impatrq/VIA/aplicacion de Gps/codigo final parte 1.jpg

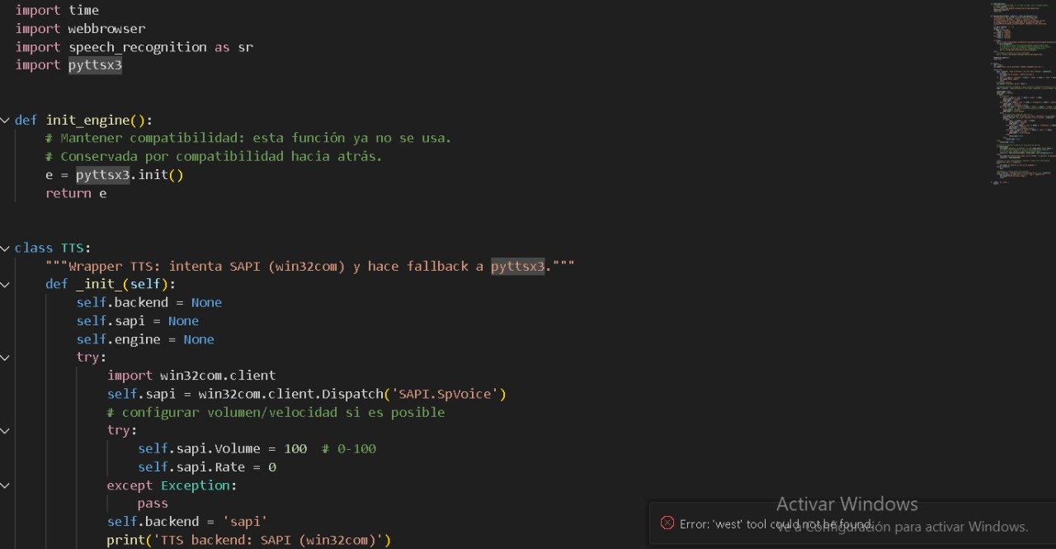
aplicacion de Gps/codigo final parte 1.jpg
