impatrq/VIA/aplicacion de Gps/codigo final parte 2.jpg

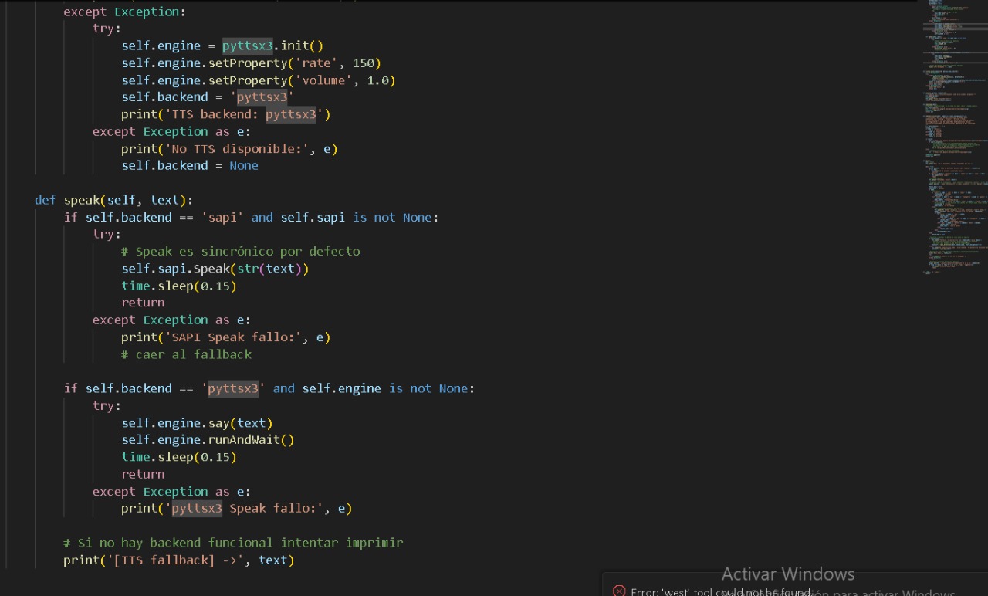
aplicacion de Gps/codigo final parte 2.jpg
