impatrq/VIA/aplicacion de Gps/codigo final parte 3.jpg

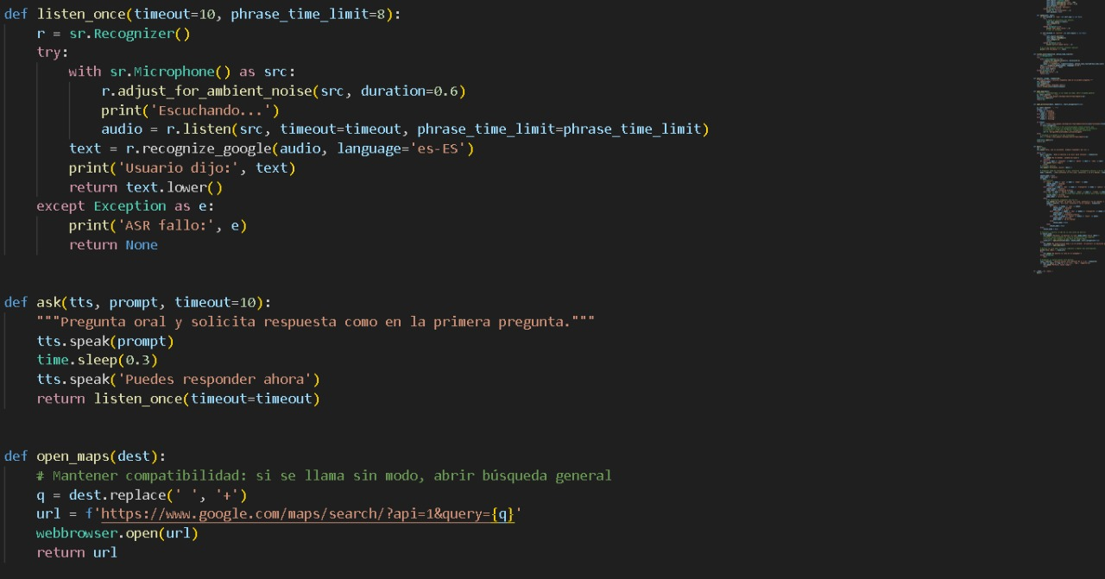
aplicacion de Gps/codigo final parte 3.jpg
