impatrq/VIA/aplicacion de Gps/inicio de codigo principal.jpg

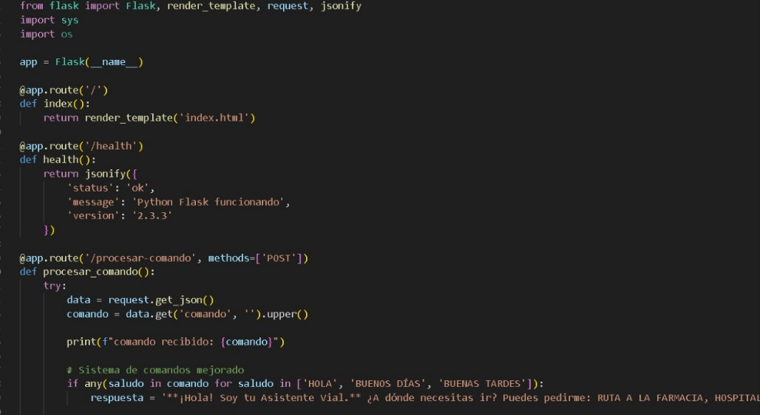
aplicacion de Gps/inicio de codigo principal.jpg
