impatrq/VIA/aplicacion de Gps/segunda parte de codigo principal.jpg

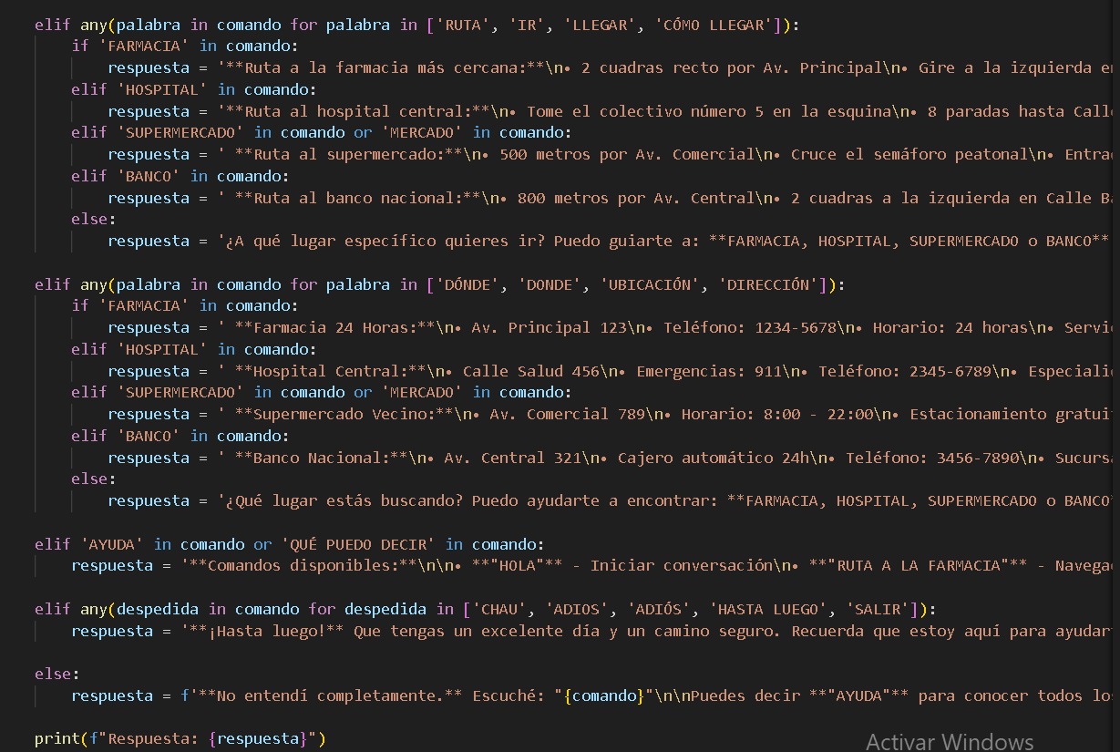
aplicacion de Gps/segunda parte de codigo principal.jpg
