impatrq/VIA/aplicacion de Gps/tercera parte de codigo principal.jpg

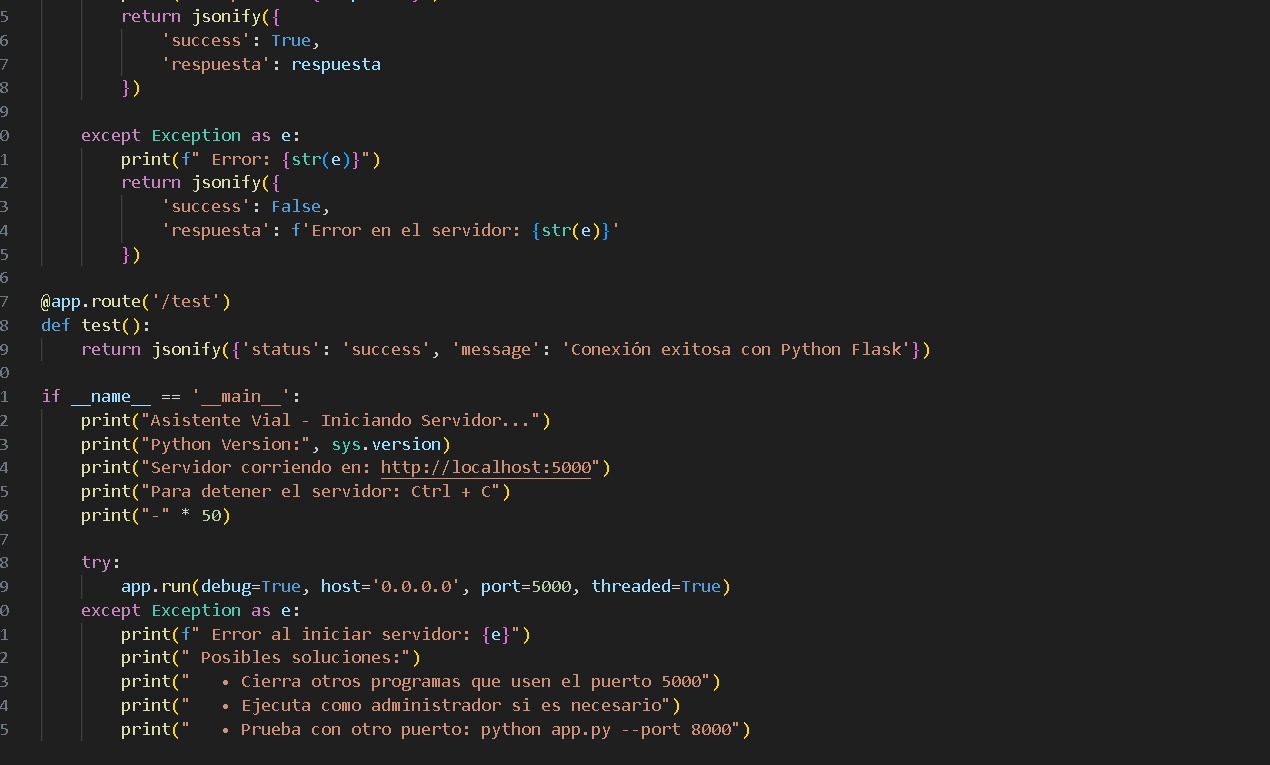
aplicacion de Gps/tercera parte de codigo principal.jpg
