impatrq/VIA/circuito de audio/pongo placa en acido.jpg

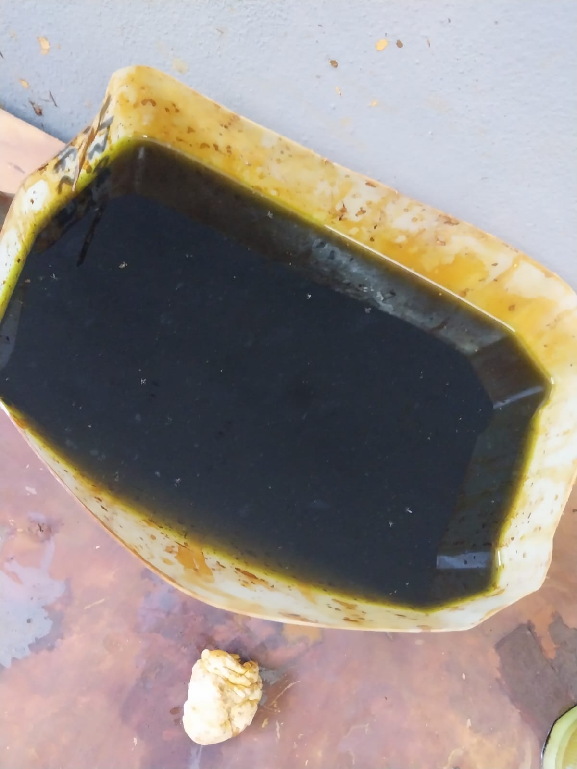
circuito de audio/pongo placa en acido.jpg
