impatrq/VIA/Compras/camara.jpg

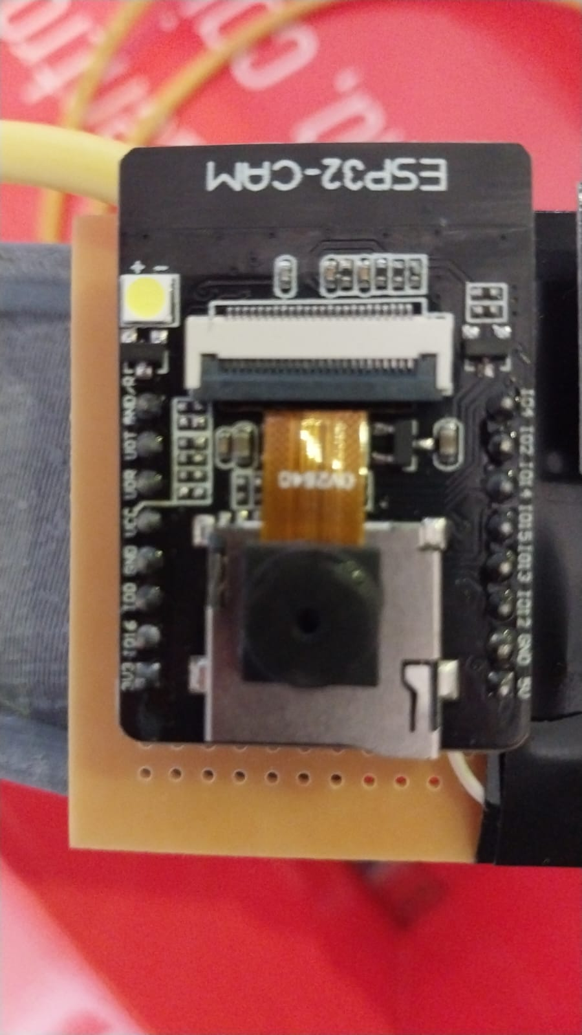
Compras/camara.jpg
