impatrq/VIA/Compras/raspberry.jpg

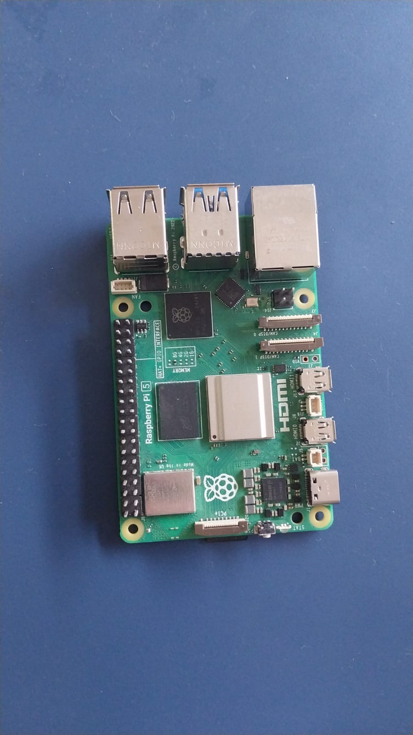
Compras/raspberry.jpg
