impatrq/VIA/Compras/sensor de px.jpg

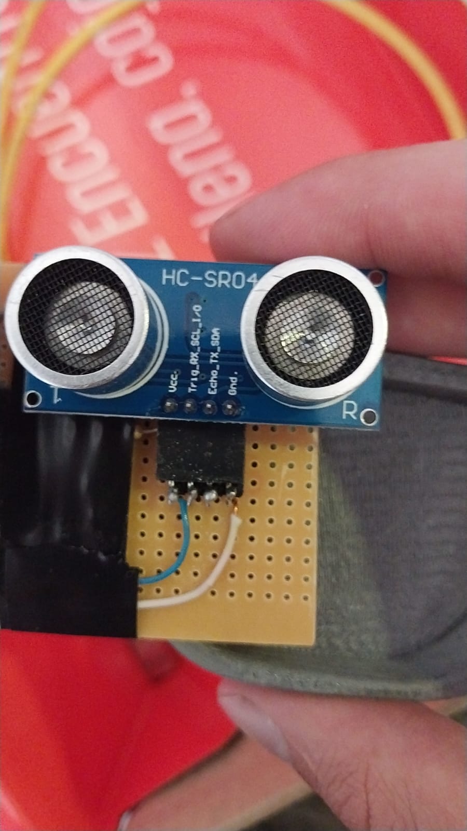
Compras/sensor de px.jpg
