impatrq/VIA/Compras/termocontra.jpg

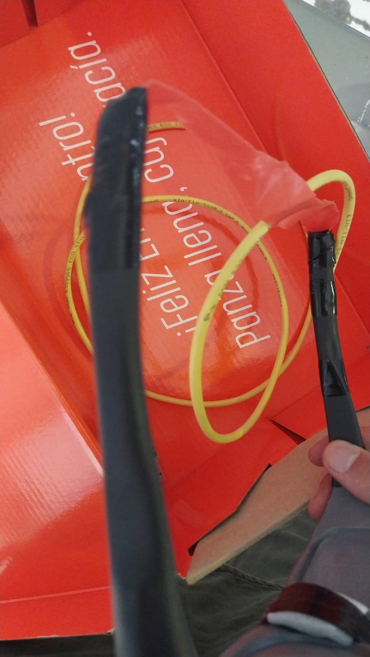
Compras/termocontra.jpg
