impatrq/VIA/Diseño de los lentes/12466696-14f5-42b8-8ee0-9e572aa3d88a.jpeg

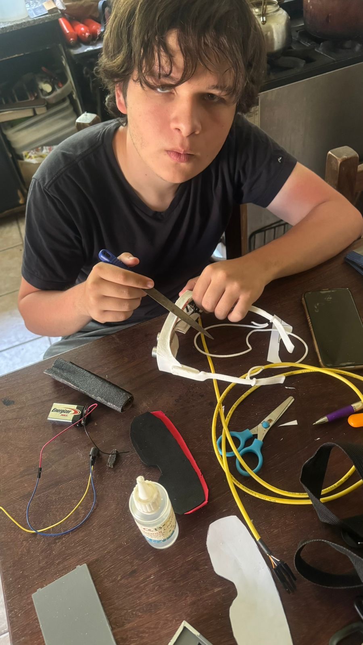
Diseño de los lentes/12466696-14f5-42b8-8ee0-9e572aa3d88a.jpeg
