impatrq/VIA/Diseño de los lentes/b83320ea-6508-4606-a873-f71e1e73f696.jpeg

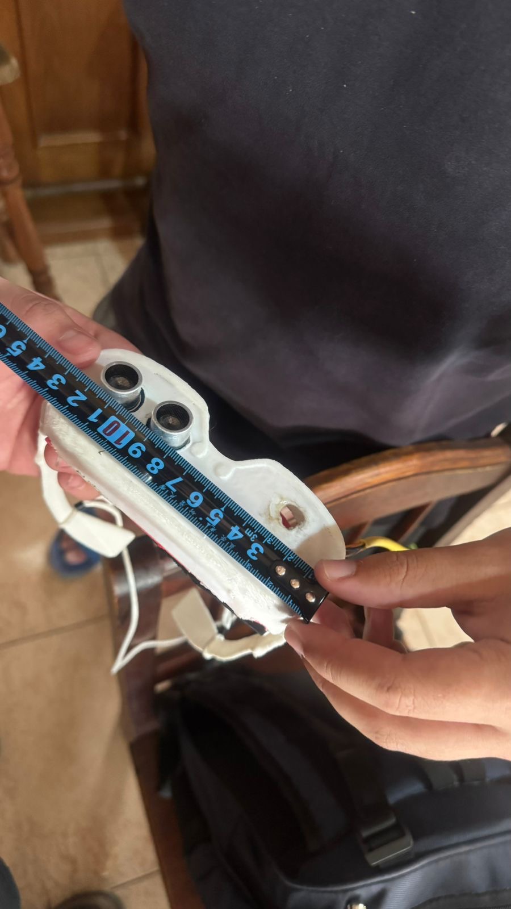
Diseño de los lentes/b83320ea-6508-4606-a873-f71e1e73f696.jpeg
