impatrq/VIA/Diseño de los lentes/primera impresion de lentes.jpg

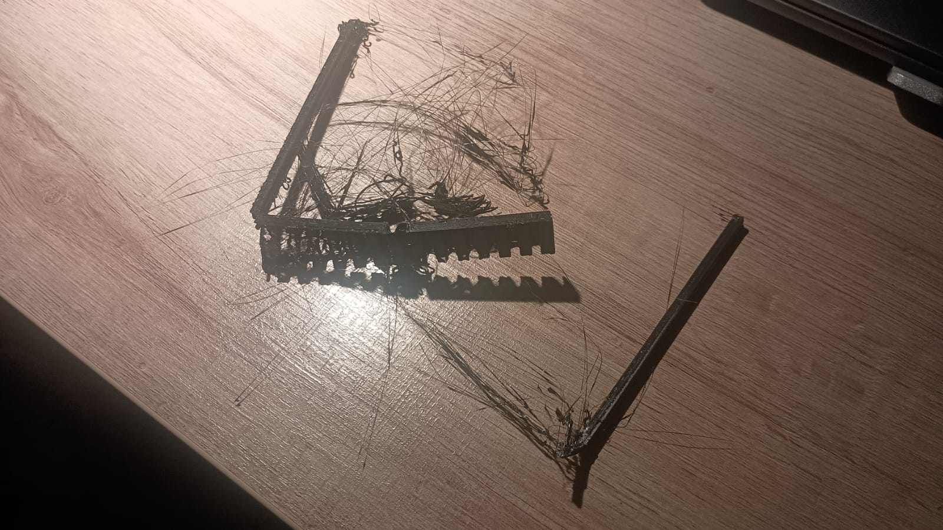
Diseño de los lentes/primera impresion de lentes.jpg
