impatrq/VIA/Diseño de los lentes/quinto diseño de lentes.jpg

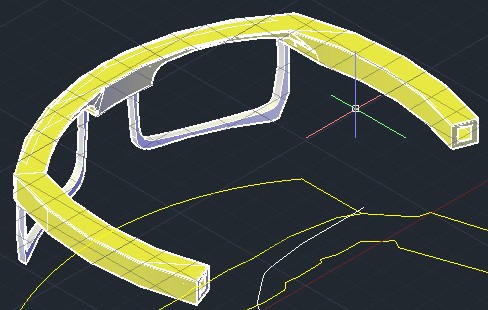
Diseño de los lentes/quinto diseño de lentes.jpg
