impatrq/VIA/Diseño de los lentes/sexto diseño de lentes.jpg

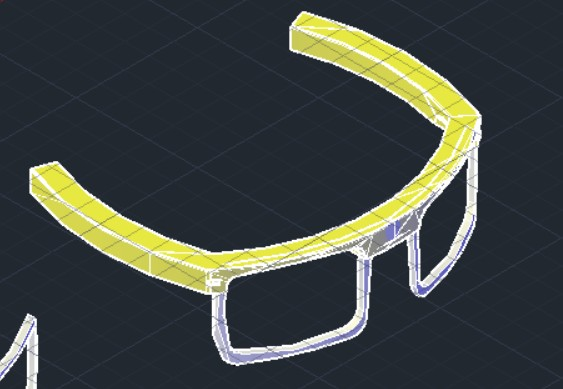
Diseño de los lentes/sexto diseño de lentes.jpg
