impatrq/VIA/Diseño de los lentes/visagras de lentes.jpg

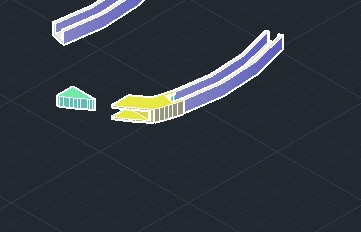
Diseño de los lentes/visagras de lentes.jpg
