impatrq/VIA/Imagenes/Auriculares/90 sin título_20251203141430.jpeg

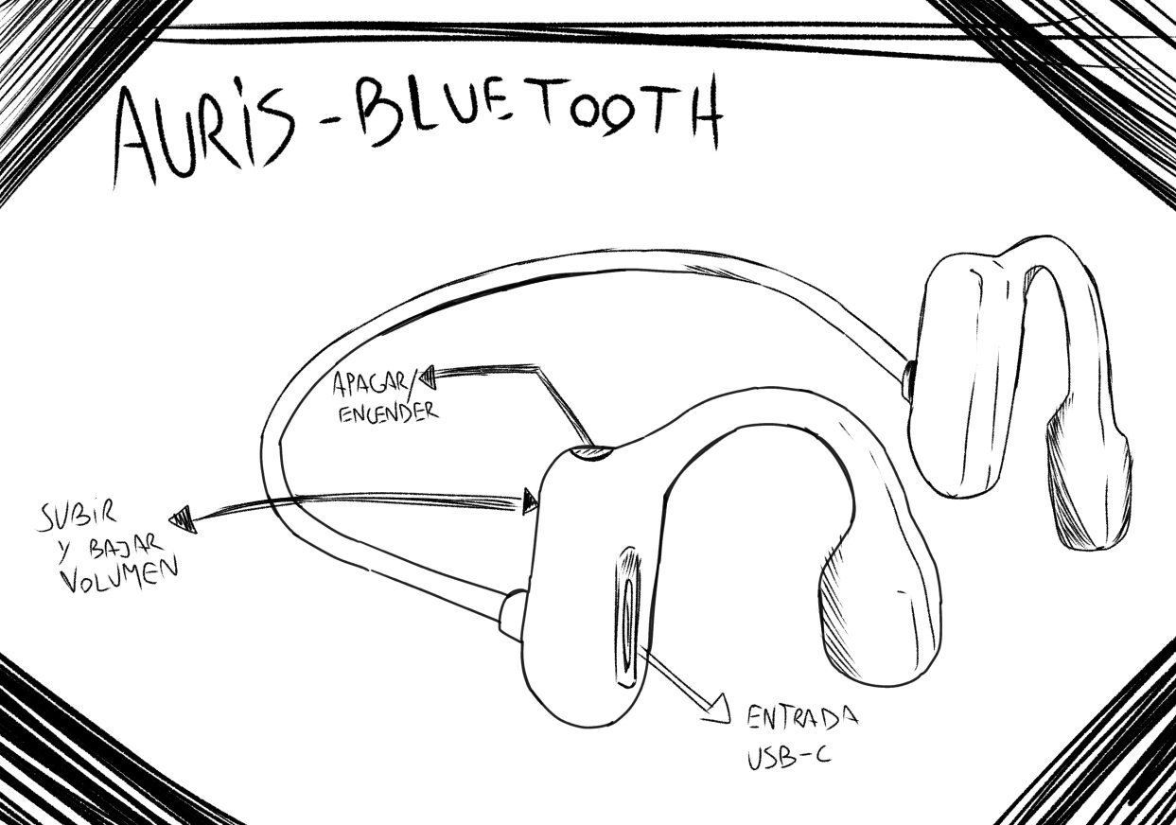
Imagenes/Auriculares/90 sin título_20251203141430.jpeg
