impatrq/VIA/Imagenes/Auriculares/WhatsApp Image 2025-12-07 at 10.33.51 PM.jpeg

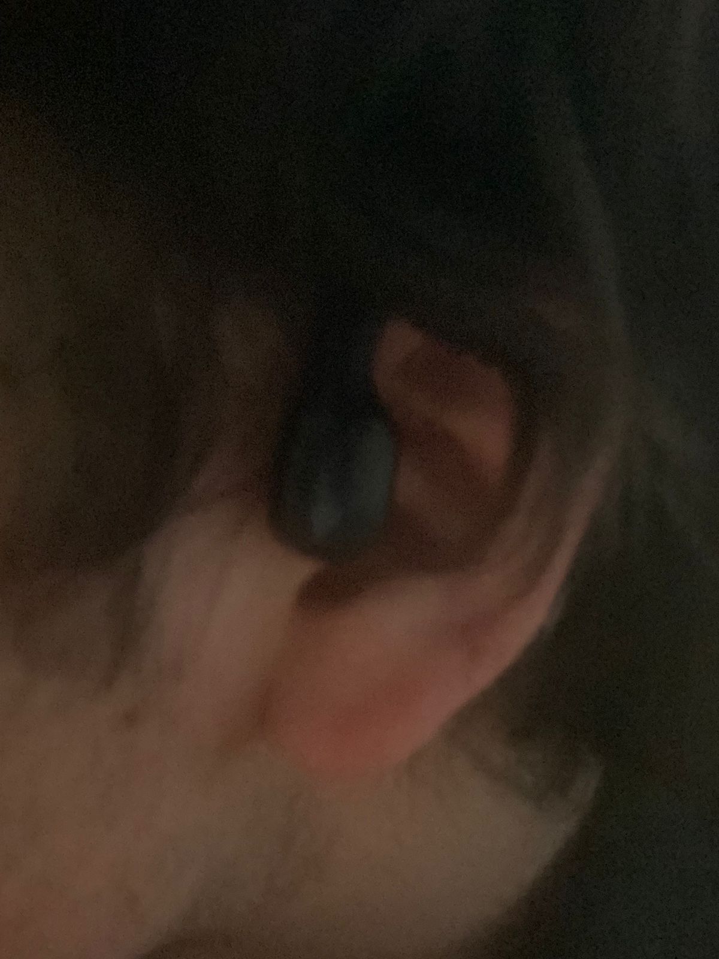
Imagenes/Auriculares/WhatsApp Image 2025-12-07 at 10.33.51 PM.jpeg
