impatrq/VIA/Imagenes/Camara/Camara.jpg

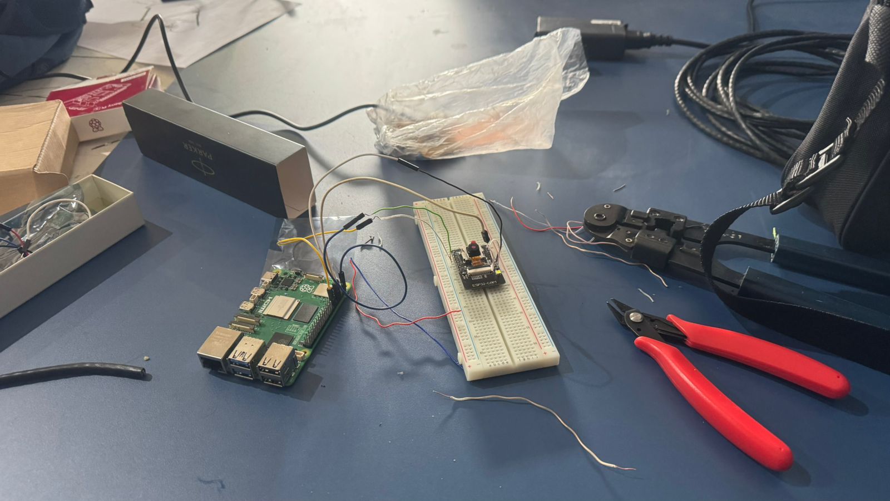
Imagenes/Camara/Camara.jpg
