impatrq/VIA/Imagenes/Foto del grupo/Bautista Paz.png

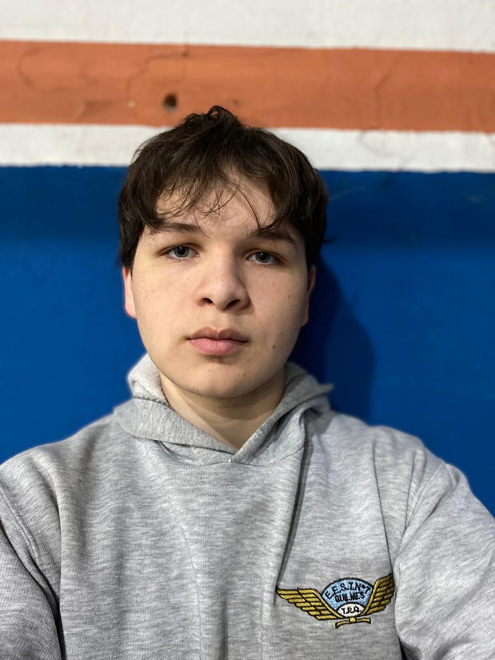
Imagenes/Foto del grupo/Bautista Paz.png
