impatrq/VIA/Imagenes/Foto del grupo/Caram Matias.png

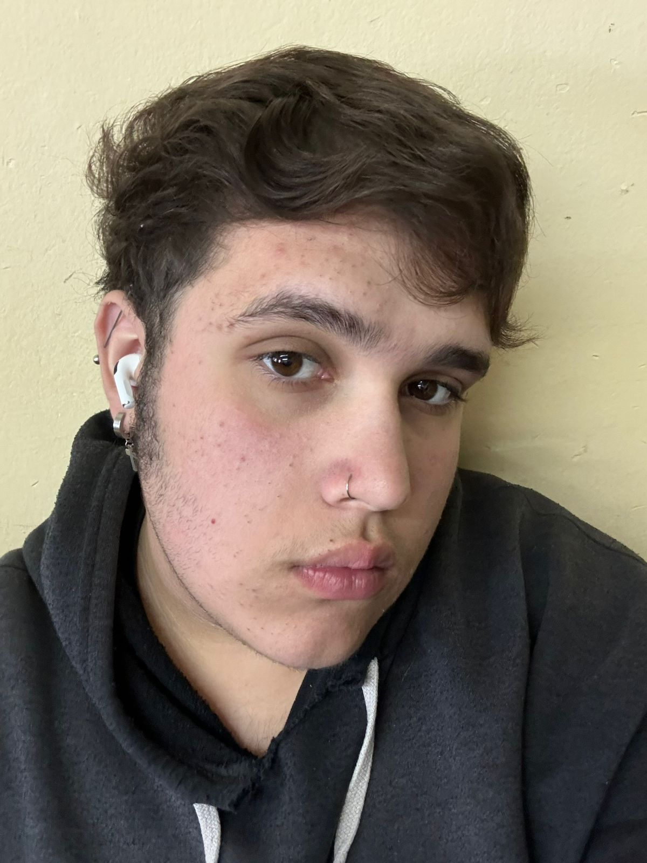
Imagenes/Foto del grupo/Caram Matias.png
