impatrq/VIA/Imagenes/Foto del grupo/Foto grupal del dia de la expo .jpg

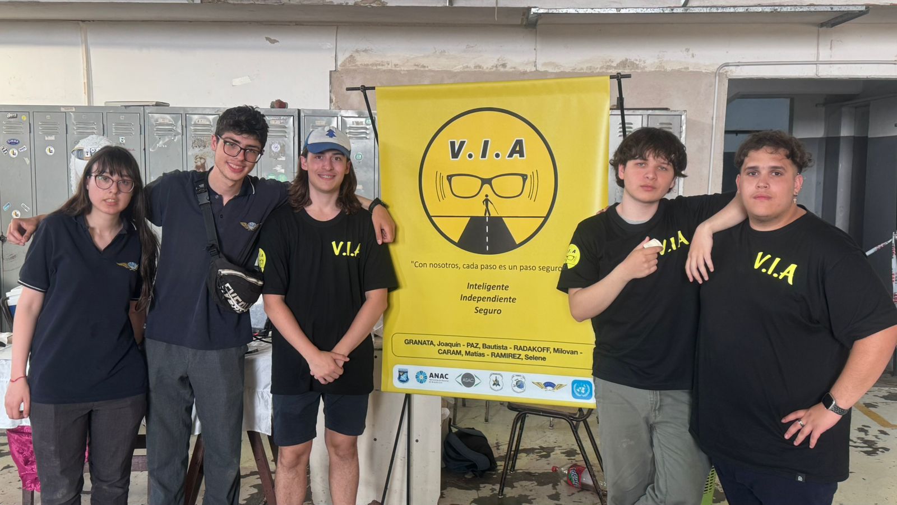
Imagenes/Foto del grupo/Foto grupal del dia de la expo .jpg
