impatrq/VIA/Imagenes/Foto del grupo/Granata Joaquin.png

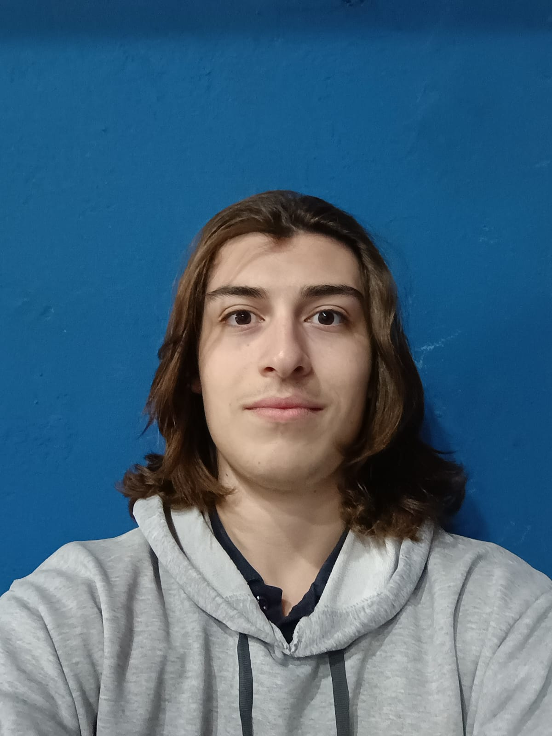
Imagenes/Foto del grupo/Granata Joaquin.png
