impatrq/VIA/Imagenes/Foto del grupo/Radakoff Milovan.png

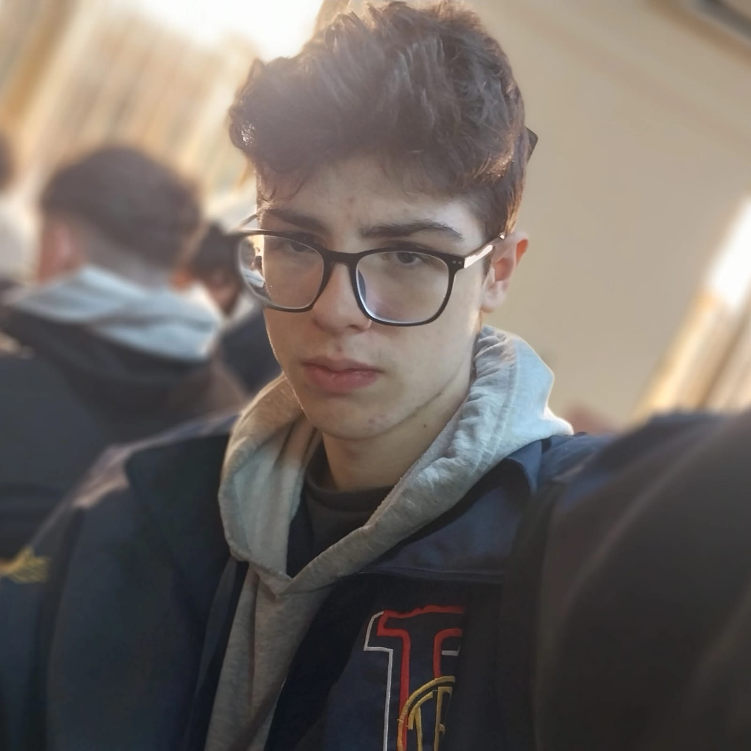
Imagenes/Foto del grupo/Radakoff Milovan.png
