impatrq/VIA/Imagenes/Lentes/Corte de filamento en la reimpresion 2.3.jpg

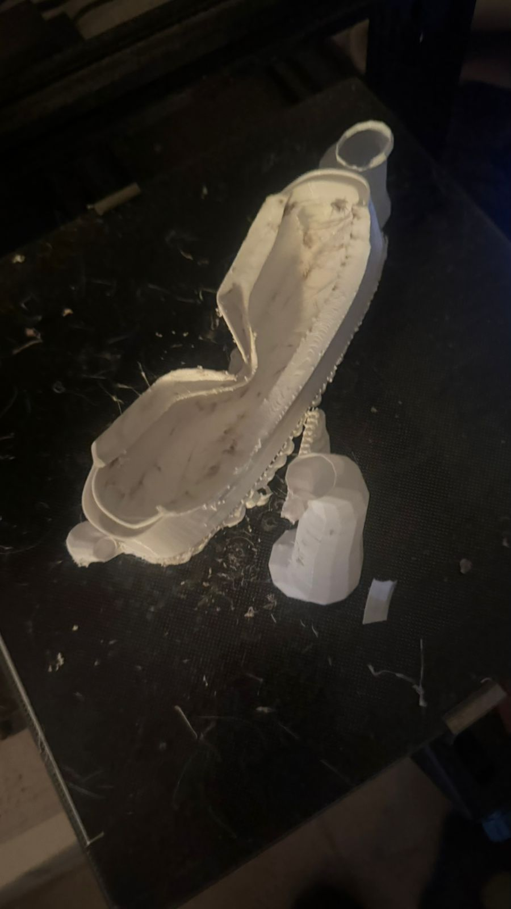
Imagenes/Lentes/Corte de filamento en la reimpresion 2.3.jpg
