impatrq/VIA/Imagenes/Lentes/Fallo de la 1ra impresion.jpg

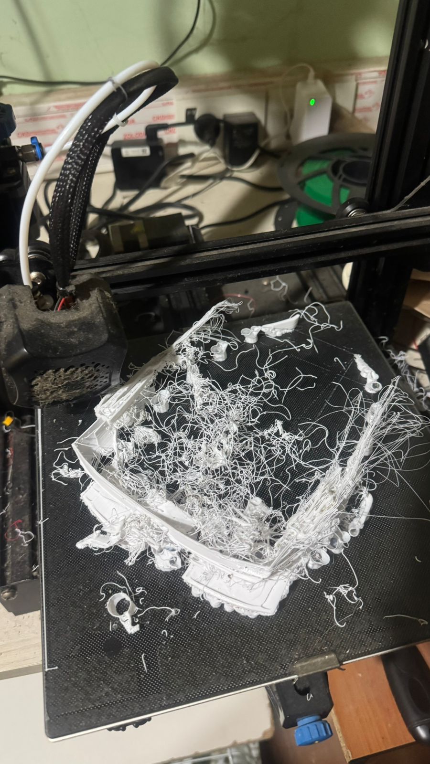
Imagenes/Lentes/Fallo de la 1ra impresion.jpg
