impatrq/VIA/Imagenes/Lentes/Fallo impresion 3.0.jpg

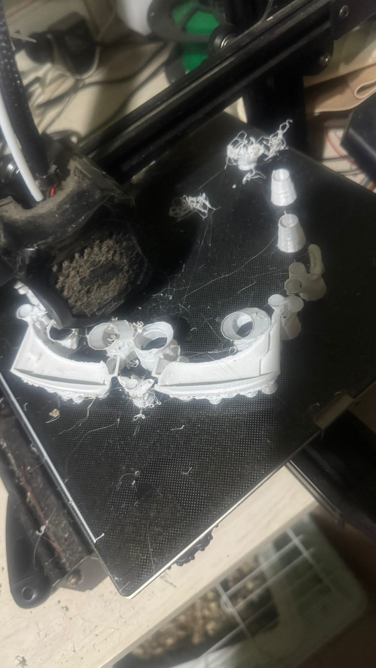
Imagenes/Lentes/Fallo impresion 3.0.jpg
