impatrq/VIA/Imagenes/Lentes/image.png

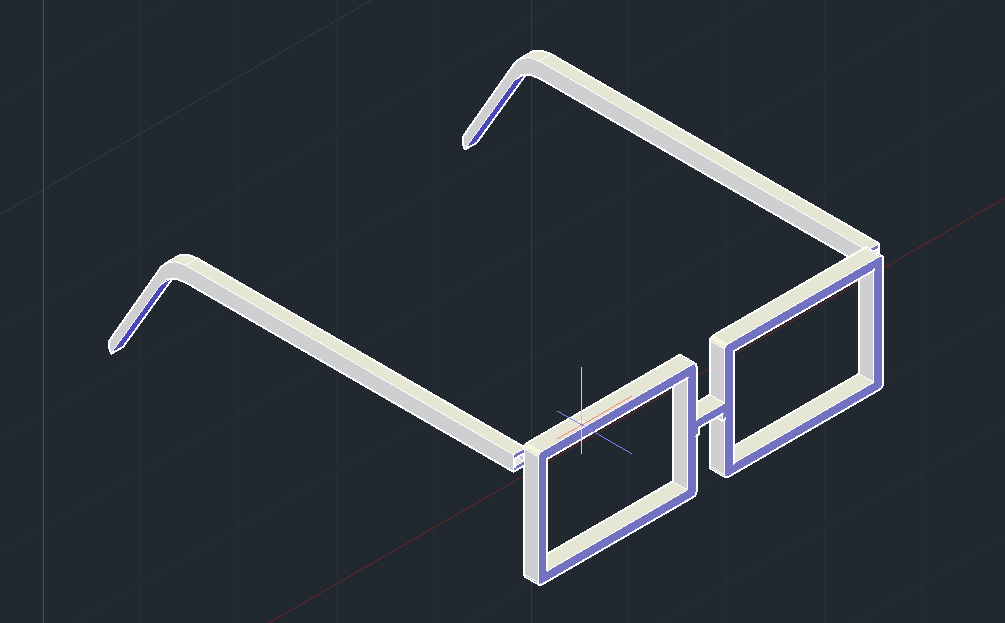
Imagenes/Lentes/image.png
