impatrq/VIA/Imagenes/Lentes/Impresion modelo 2.3.jpg

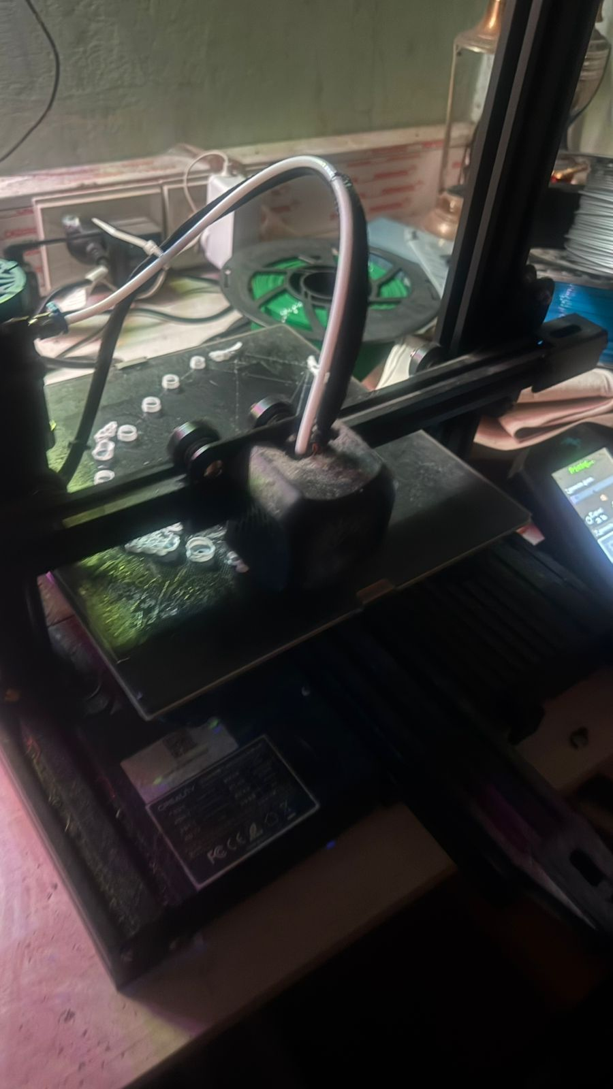
Imagenes/Lentes/Impresion modelo 2.3.jpg
