impatrq/VIA/Imagenes/Lentes/Lentes V2.1 - Puestos.png

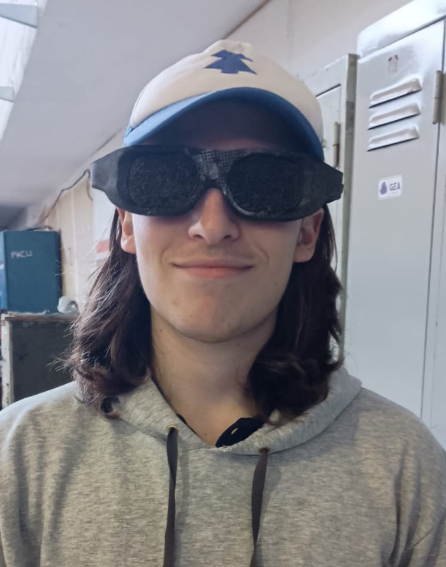
Imagenes/Lentes/Lentes V2.1 - Puestos.png
