impatrq/VIA/Imagenes/Lentes/Lentes V2.1.png

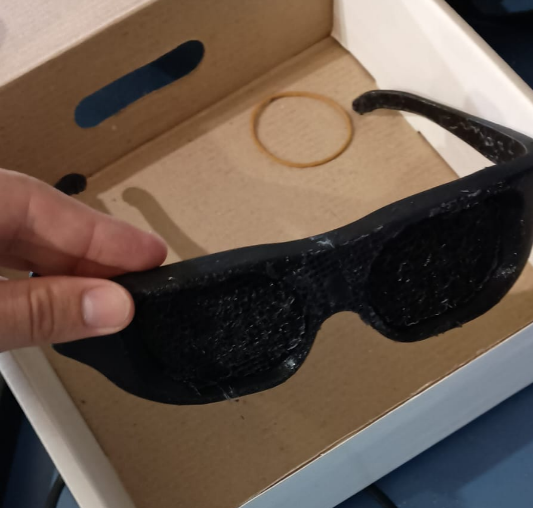
Imagenes/Lentes/Lentes V2.1.png
