impatrq/VIA/Imagenes/Lentes/Lentes V2.2.jpg

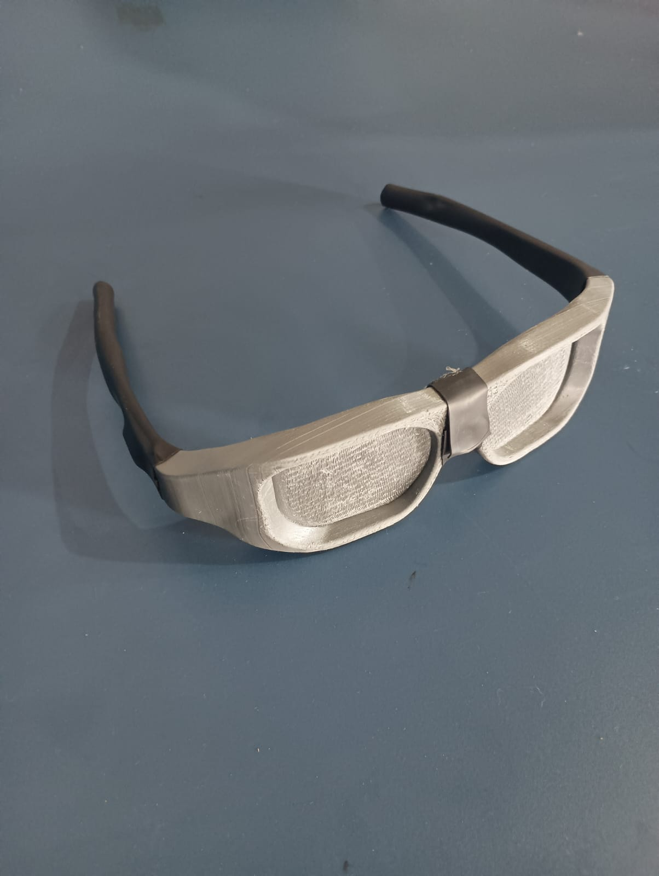
Imagenes/Lentes/Lentes V2.2.jpg
