impatrq/VIA/Imagenes/Lentes/Lentes v2.3 terminados.jpg

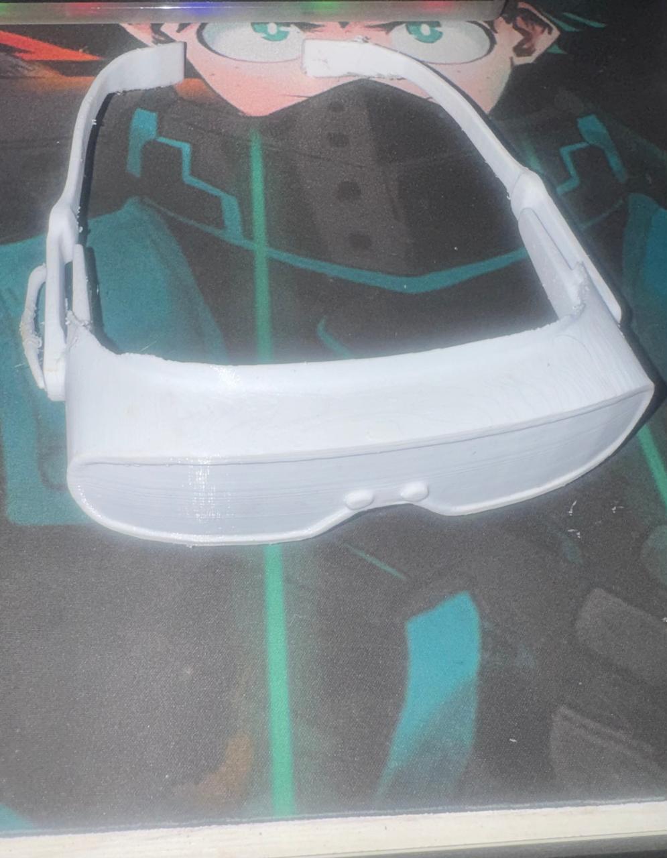
Imagenes/Lentes/Lentes v2.3 terminados.jpg
