impatrq/VIA/Imagenes/Lentes/Modelado de la caja.png

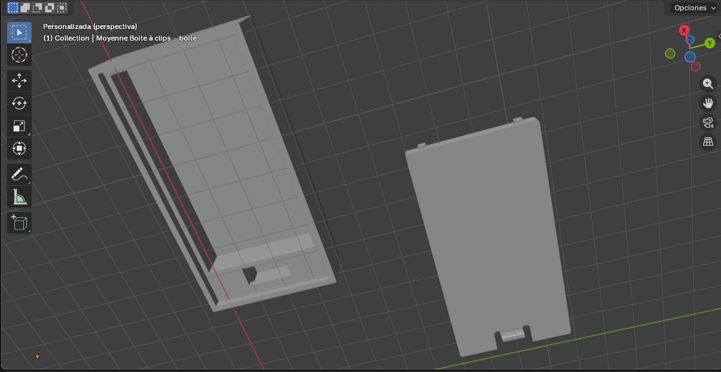
Imagenes/Lentes/Modelado de la caja.png
