impatrq/VIA/Imagenes/Lentes/Modelado de los lentes.png

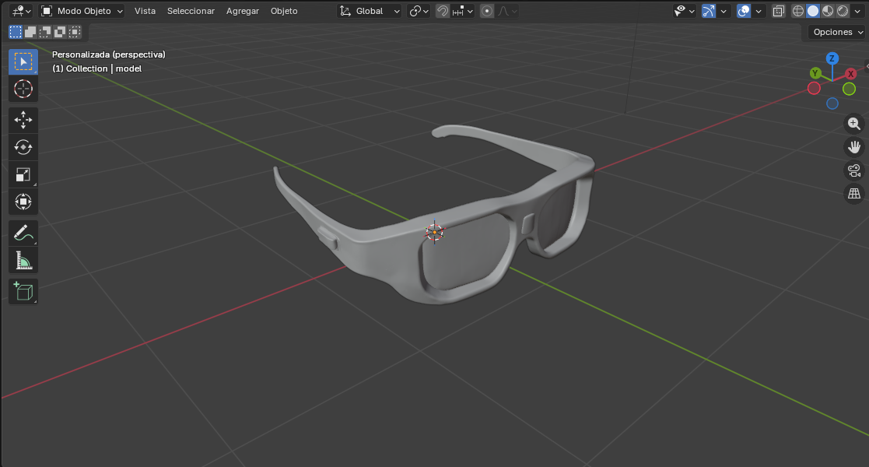
Imagenes/Lentes/Modelado de los lentes.png
