impatrq/VIA/Imagenes/Lentes/Modelo 2.3 reimprecion.png

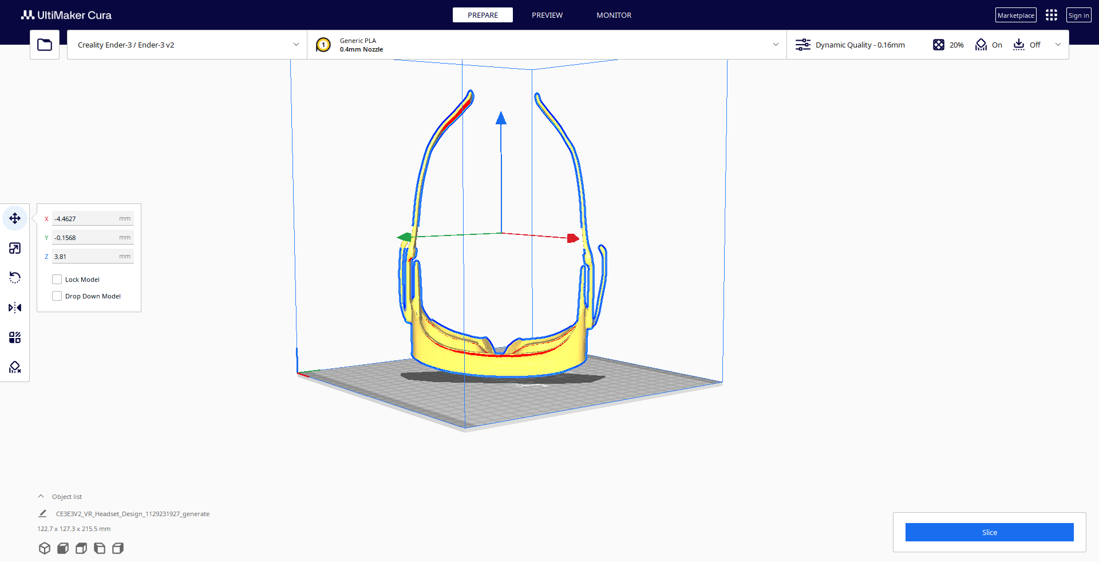
Imagenes/Lentes/Modelo 2.3 reimprecion.png
