impatrq/VIA/Imagenes/Lentes/Modelo 2.3.png

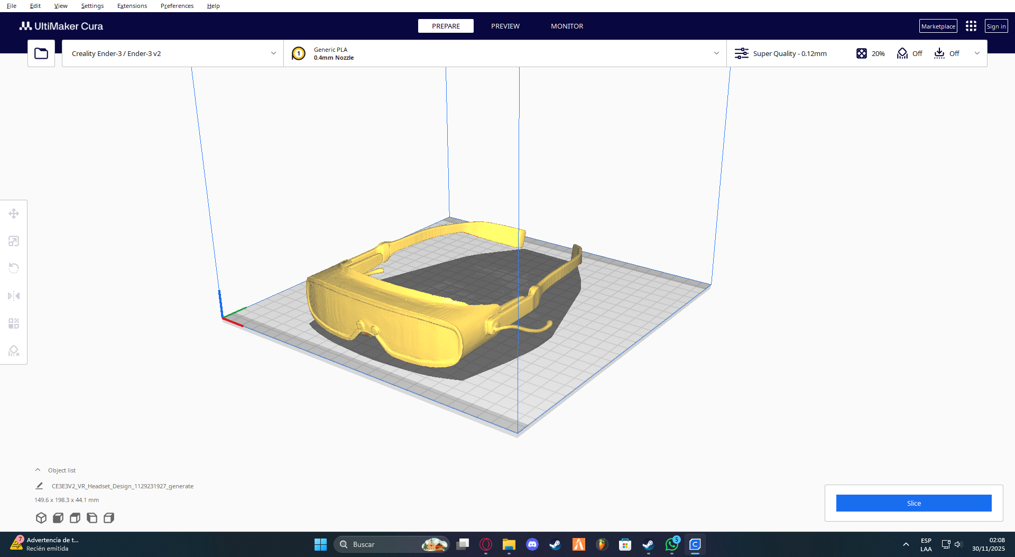
Imagenes/Lentes/Modelo 2.3.png
