impatrq/VIA/Imagenes/Lentes/Modelo 3.0.png

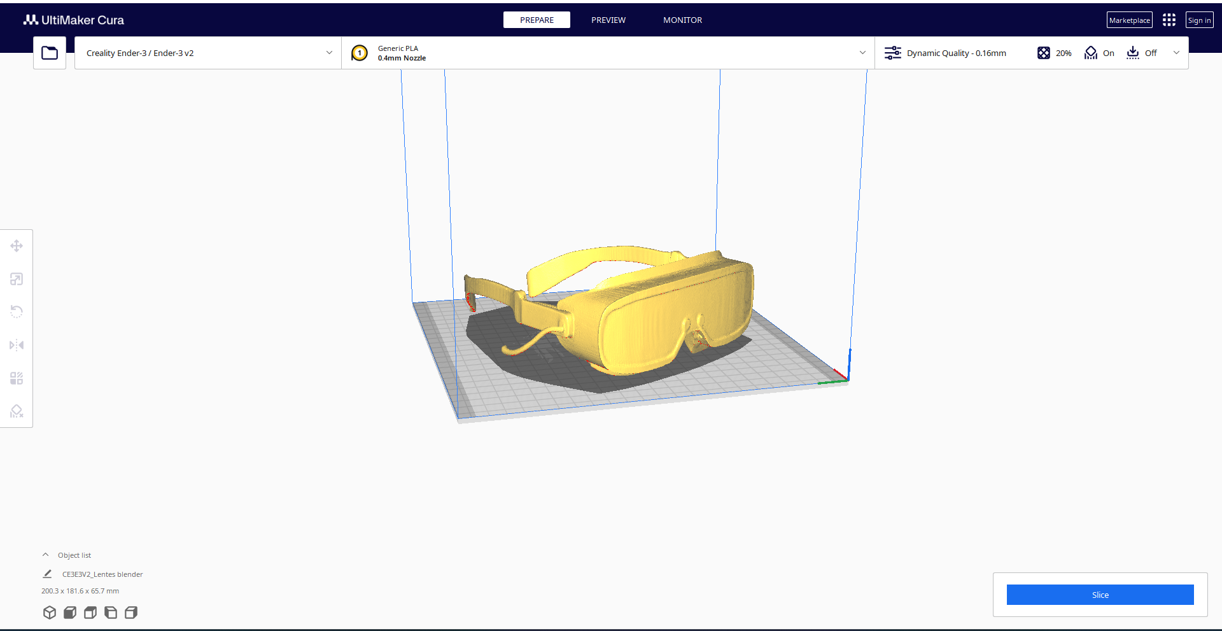
Imagenes/Lentes/Modelo 3.0.png
