impatrq/VIA/Imagenes/Lentes/Modelo terminado v2.3.png

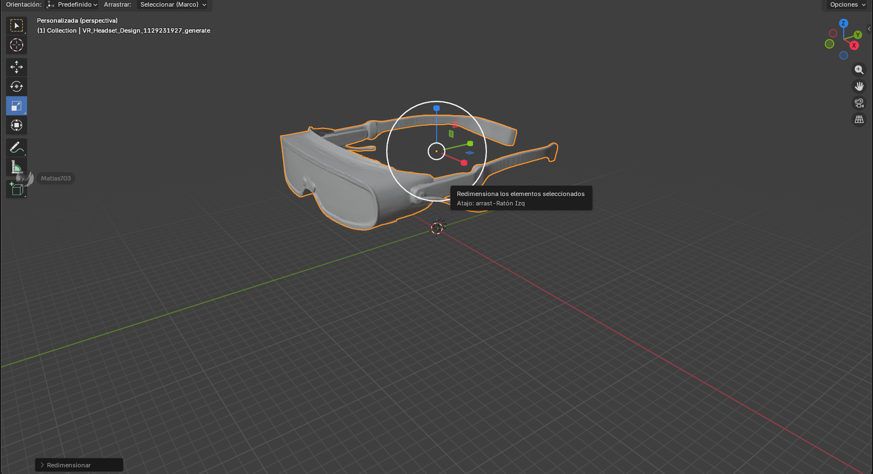
Imagenes/Lentes/Modelo terminado v2.3.png
