impatrq/VIA/Imagenes/Lentes/Modelo terminado v3.0.png

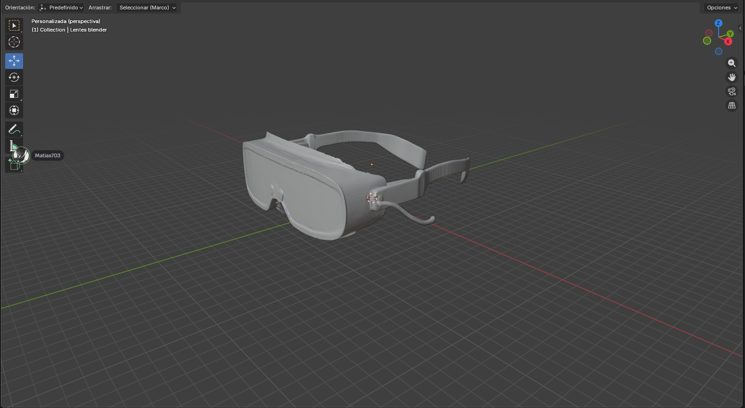
Imagenes/Lentes/Modelo terminado v3.0.png
