impatrq/VIA/Imagenes/Lentes/Nuevo inicio 3.0.jpg

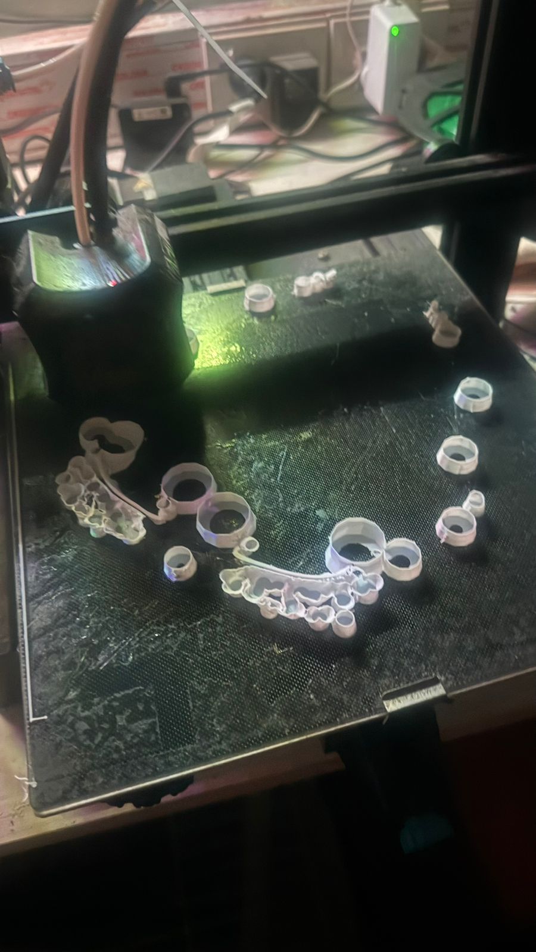
Imagenes/Lentes/Nuevo inicio 3.0.jpg
