impatrq/VIA/Imagenes/Lentes/Reimpresion modelo 2.3.jpg

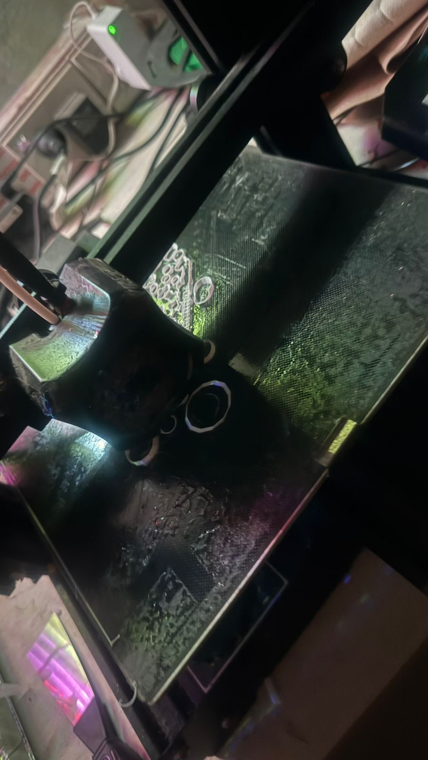
Imagenes/Lentes/Reimpresion modelo 2.3.jpg
