impatrq/VIA/Imagenes/Lentes/WhatsApp Image 2025-11-18 at 2.41.04 PM.jpeg

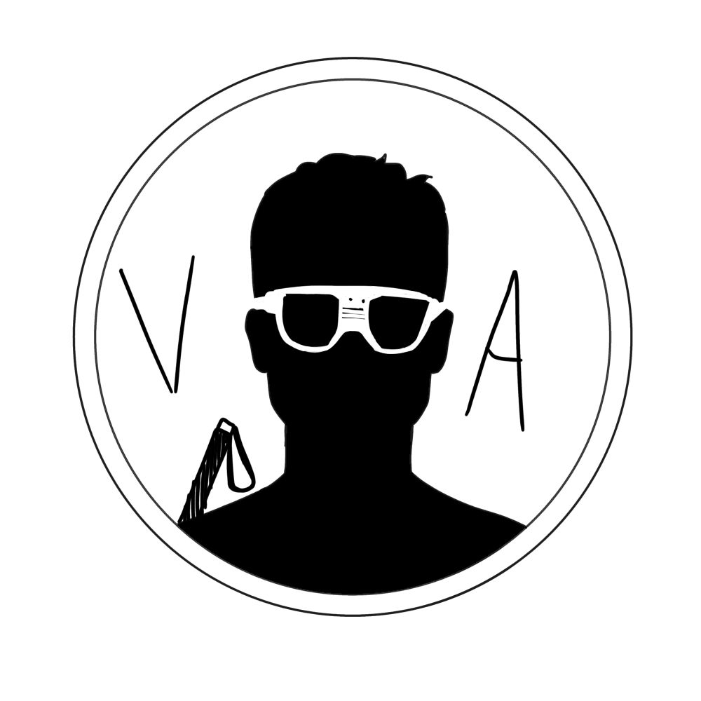
Imagenes/Lentes/WhatsApp Image 2025-11-18 at 2.41.04 PM.jpeg
