impatrq/VIA/Imagenes/Lentes/WhatsApp Image 2025-11-18 at 4.18.59 PM.jpeg

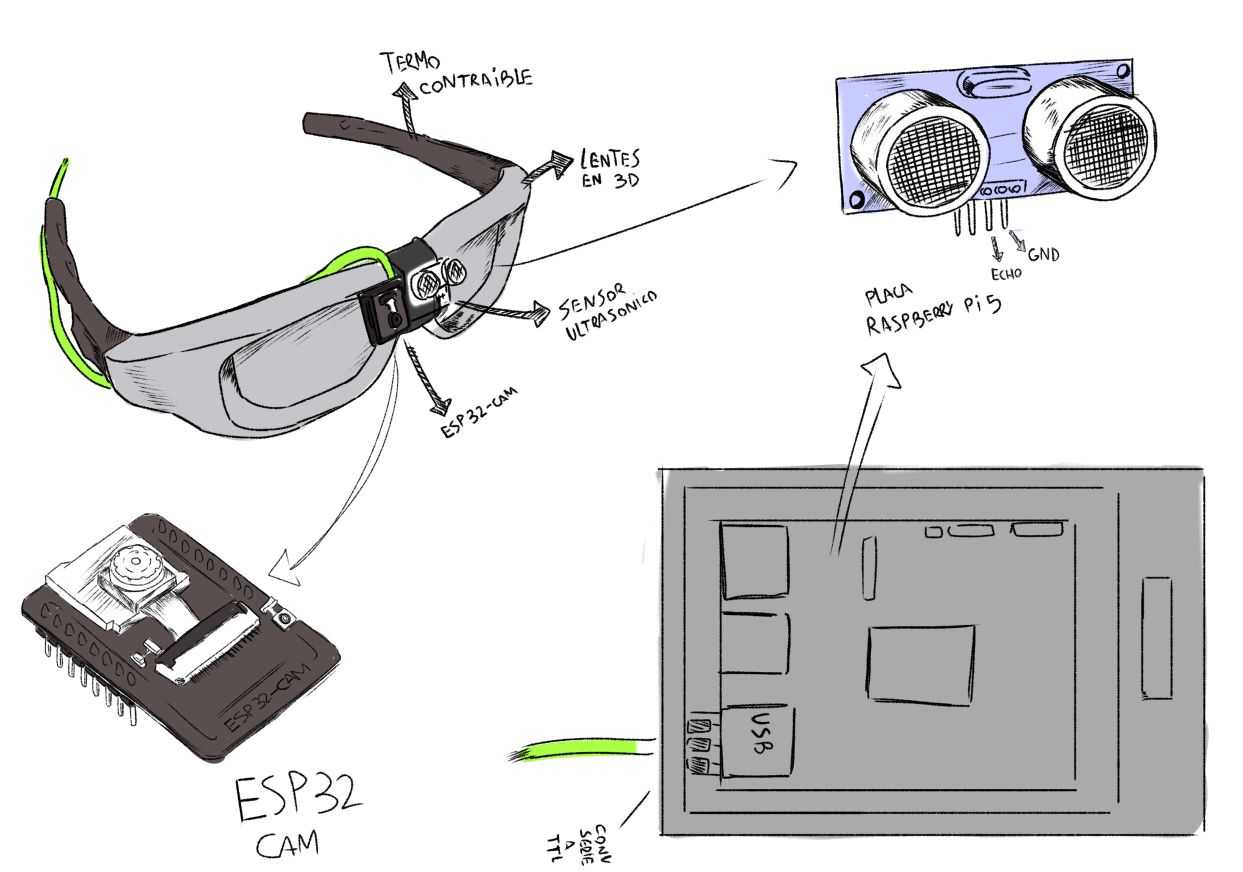
Imagenes/Lentes/WhatsApp Image 2025-11-18 at 4.18.59 PM.jpeg
