impatrq/VIA/Imagenes/Pagina web y de asistencia/Asistencia (A futuro)/BE MY EYES.jpg

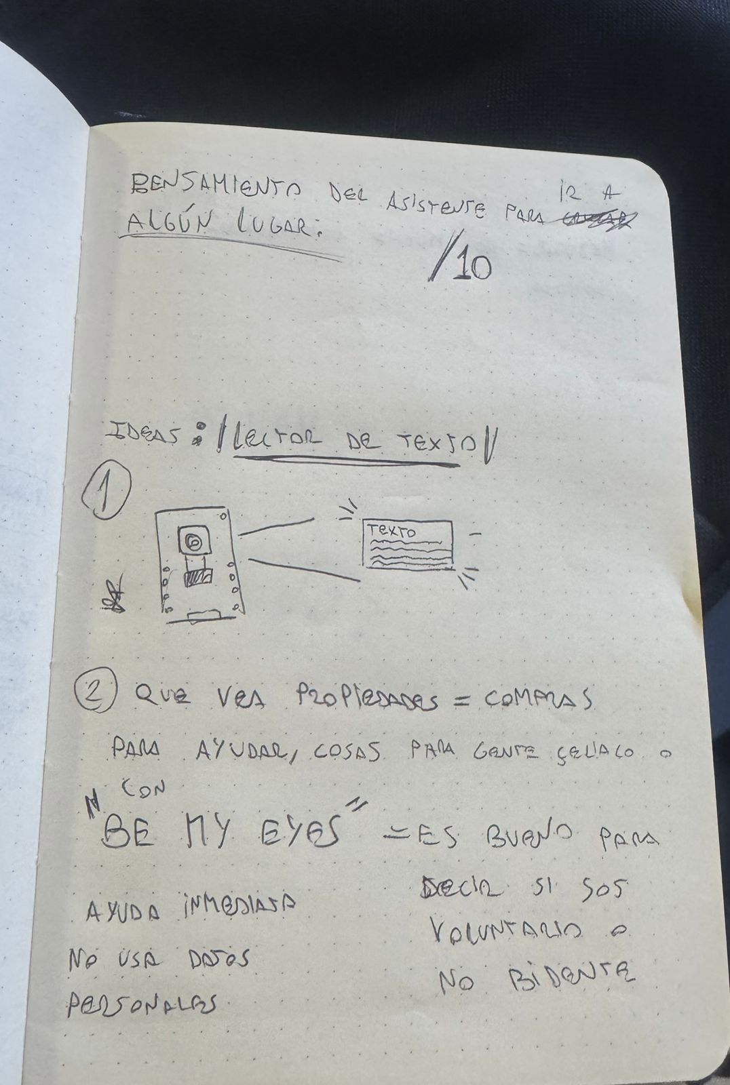
Imagenes/Pagina web y de asistencia/Asistencia (A futuro)/BE MY EYES.jpg
