impatrq/VIA/Imagenes/Pagina web y de asistencia/Pagian de asistencia/Interfaz Area de acción.png

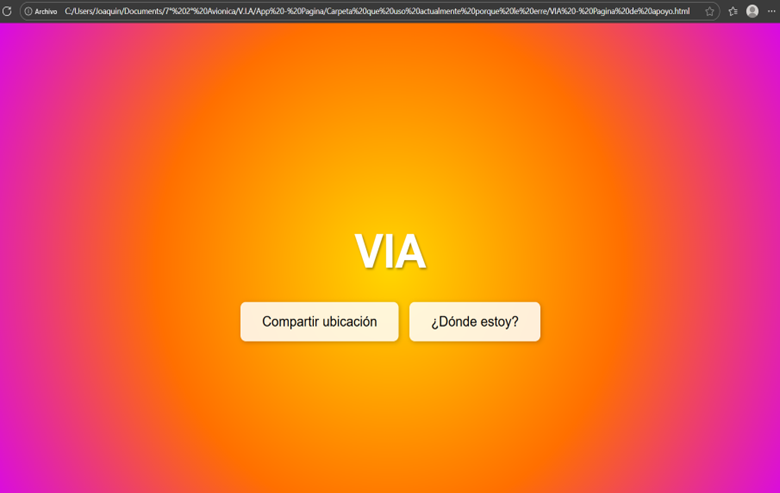
Imagenes/Pagina web y de asistencia/Pagian de asistencia/Interfaz Area de acción.png
