impatrq/VIA/Imagenes/Pagina web y de asistencia/Pagian Web/Apartado de agradecimiento.png

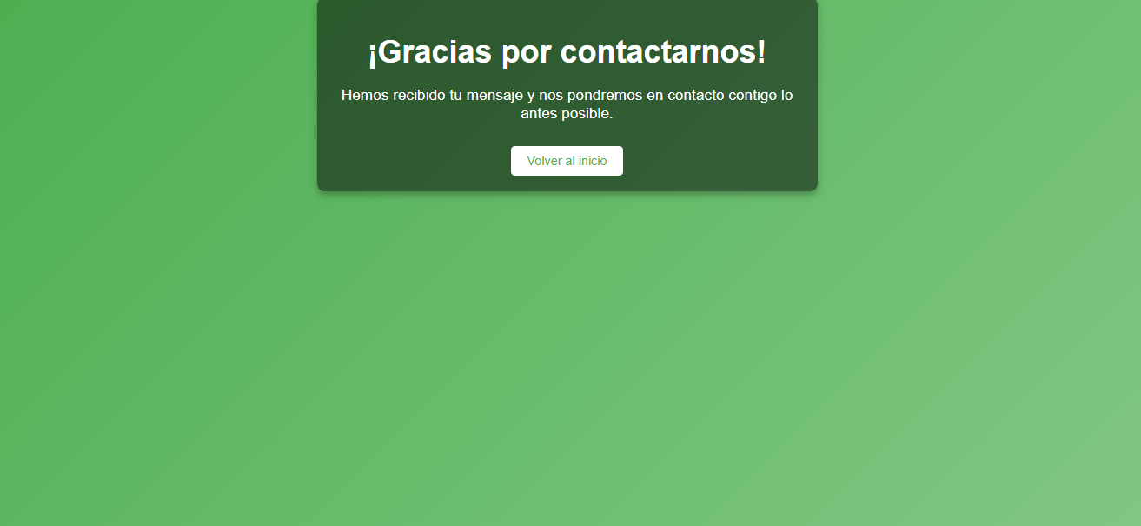
Imagenes/Pagina web y de asistencia/Pagian Web/Apartado de agradecimiento.png
