impatrq/VIA/Imagenes/Pagina web y de asistencia/Pagian Web/Apartado de contacto.png

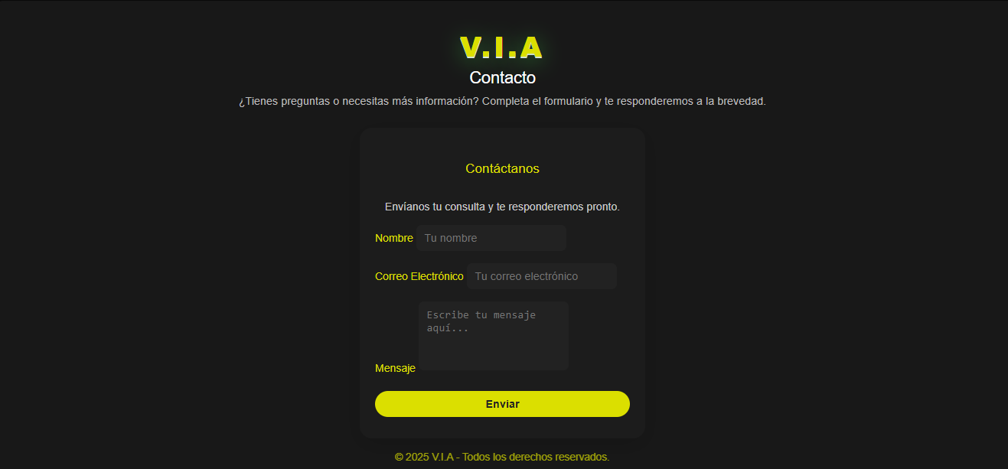
Imagenes/Pagina web y de asistencia/Pagian Web/Apartado de contacto.png
