impatrq/VIA/Imagenes/Pagina web y de asistencia/Pagian Web/Apartado de producto.png

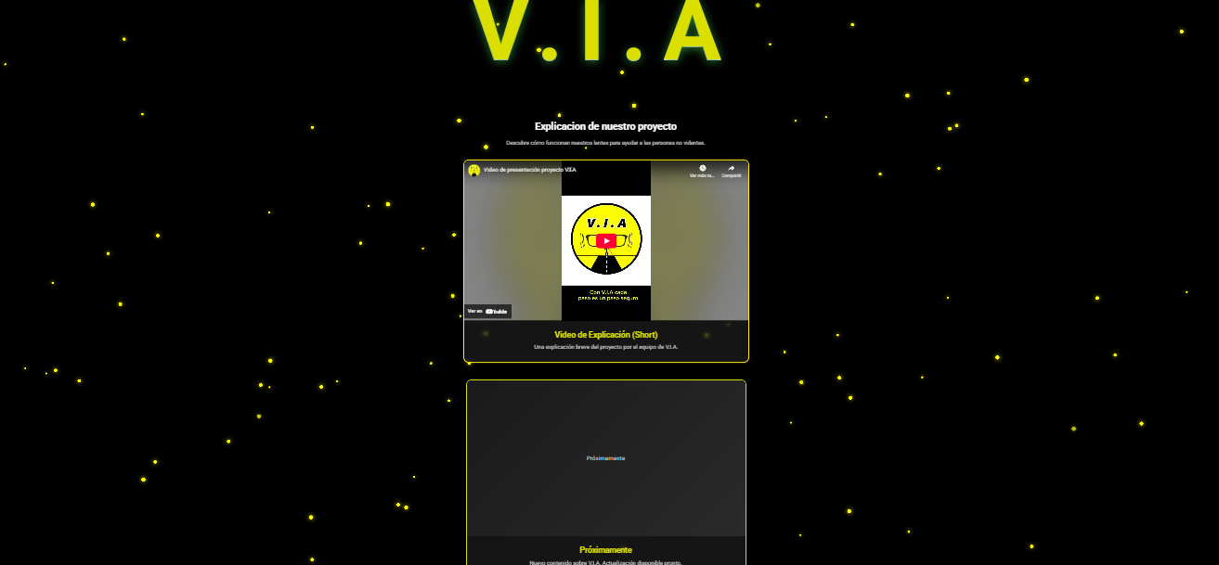
Imagenes/Pagina web y de asistencia/Pagian Web/Apartado de producto.png
