impatrq/VIA/Imagenes/Pagina web y de asistencia/Pagian Web/Caracteristicas.png

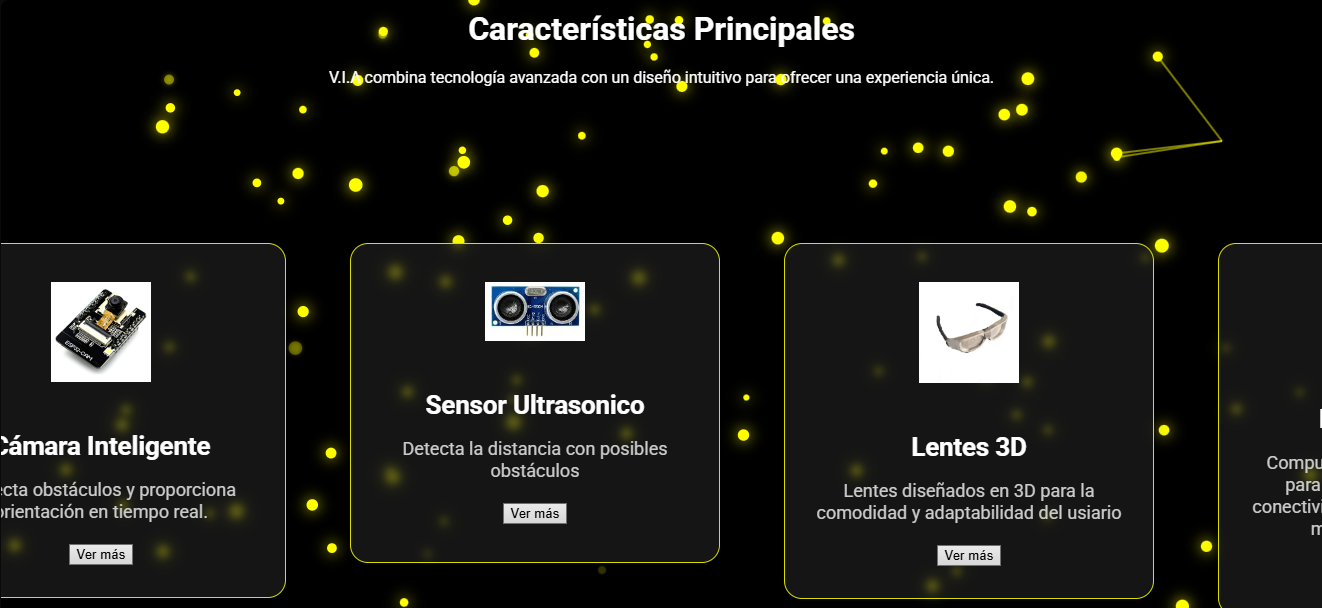
Imagenes/Pagina web y de asistencia/Pagian Web/Caracteristicas.png
