impatrq/VIA/Imagenes/Pagina web y de asistencia/Pagian Web/Encabezado.jpg

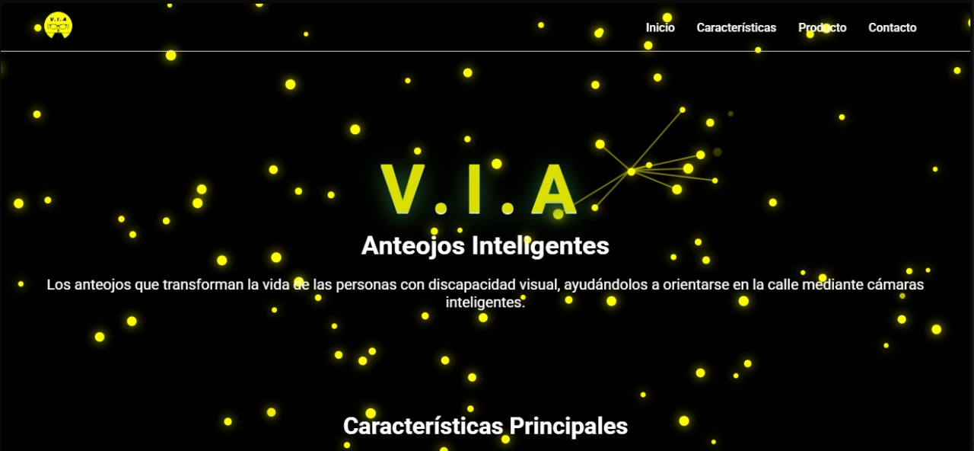
Imagenes/Pagina web y de asistencia/Pagian Web/Encabezado.jpg
