impatrq/VIA/Imagenes/Pagina web y de asistencia/Pagian Web/Modelo 3d de la pagina.png

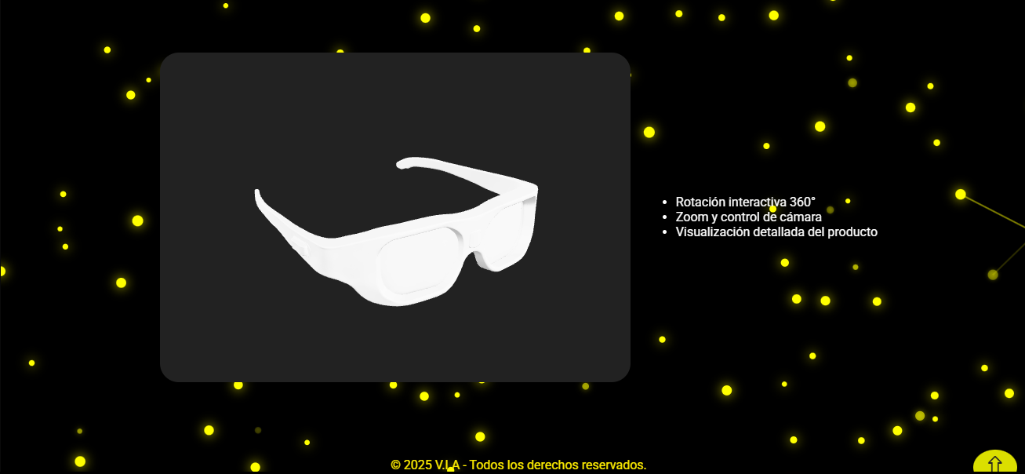
Imagenes/Pagina web y de asistencia/Pagian Web/Modelo 3d de la pagina.png
