impatrq/VIA/Imagenes/Proceso/Intento de programacion de una IA.jpg

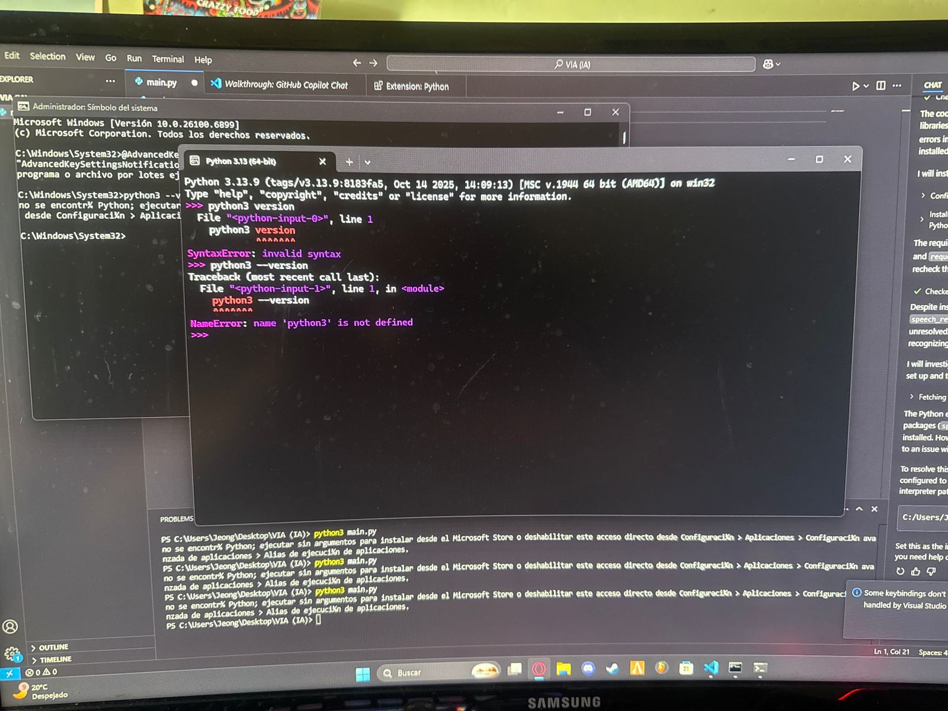
Imagenes/Proceso/Intento de programacion de una IA.jpg
