impatrq/VIA/Imagenes/Proceso/Programación - Granata - VIA.png

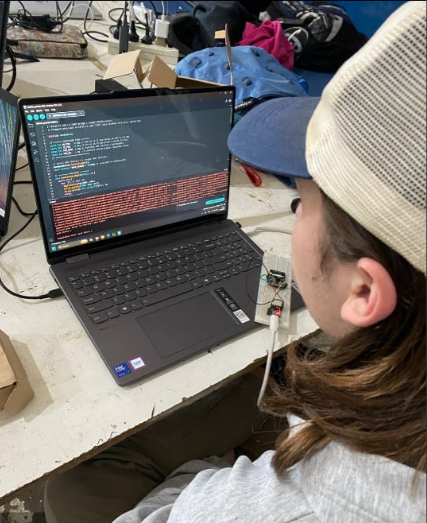
Imagenes/Proceso/Programación - Granata - VIA.png
