impatrq/VIA/Imagenes/Proceso/Soldado de los auriculares .jpg

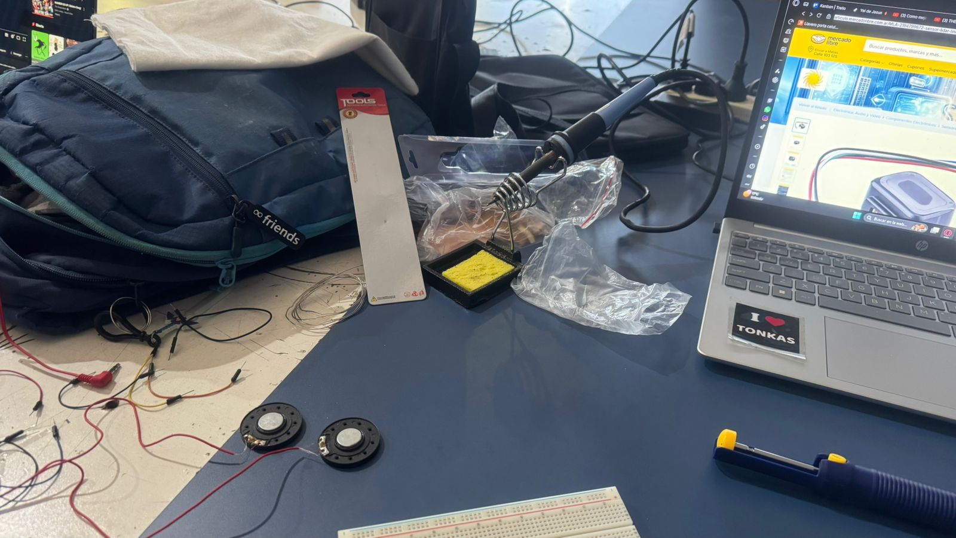
Imagenes/Proceso/Soldado de los auriculares .jpg
