impatrq/VIA/circuito de audio/soldadura de componentes.jpg

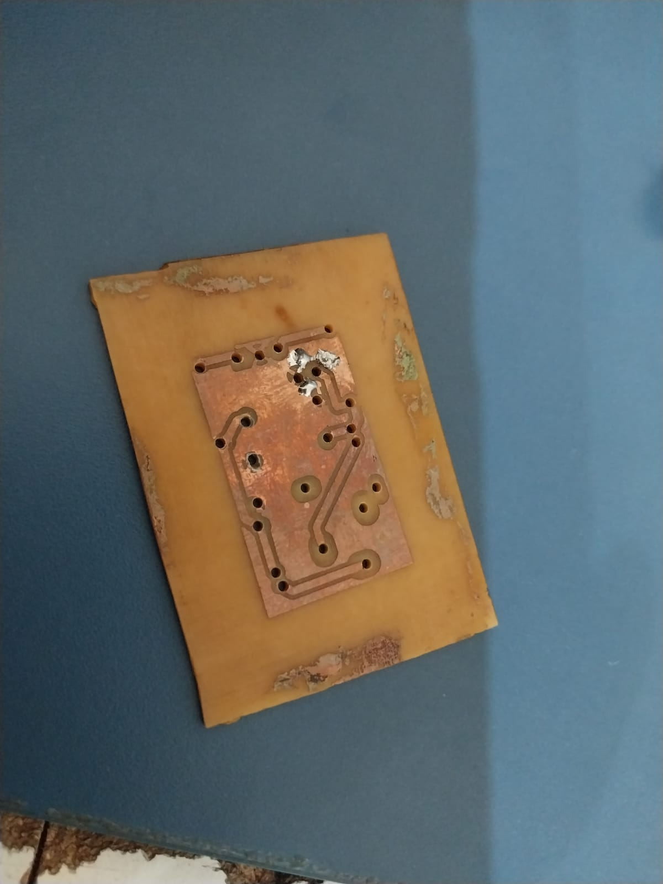
circuito de audio/soldadura de componentes.jpg
