impatrq/VIA/circuito de audio/ubicacion de componentes.jpg

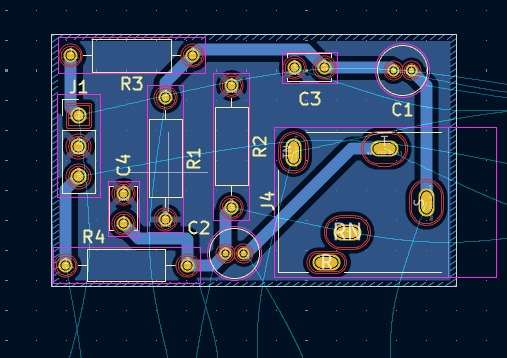
circuito de audio/ubicacion de componentes.jpg
