impatrq/VIA/Compras/componentes.jpg

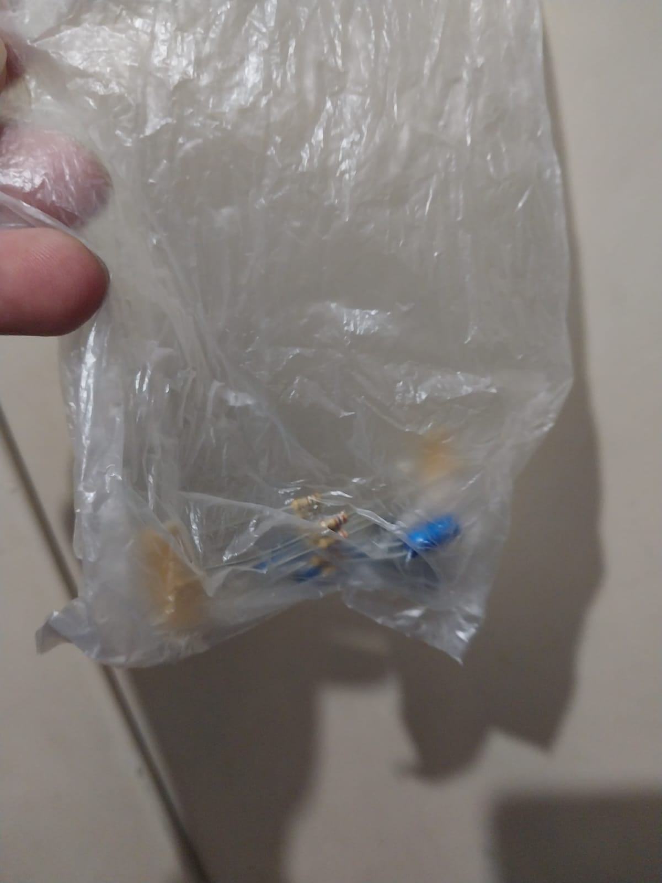
Compras/componentes.jpg
