impatrq/VIA/Imagenes/Lentes/Proyecto ensamblado y funcional.jpg

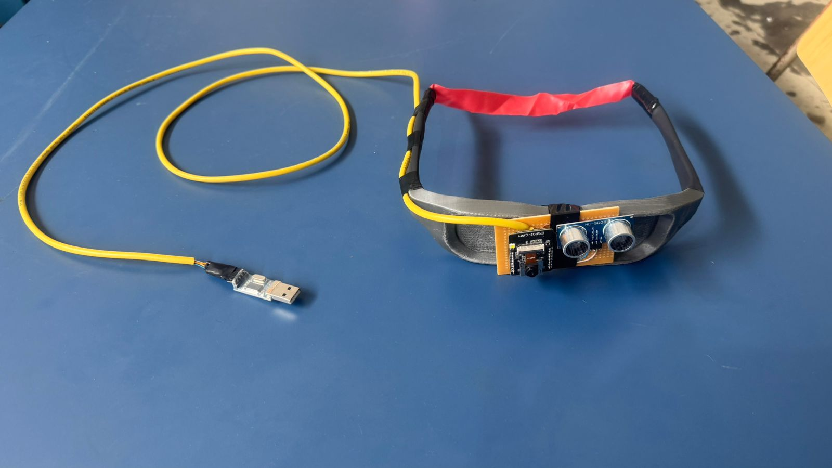
Imagenes/Lentes/Proyecto ensamblado y funcional.jpg
