impatrq/VIA/Imagenes/Camara/Prueba de la camara en protoboard.jpg

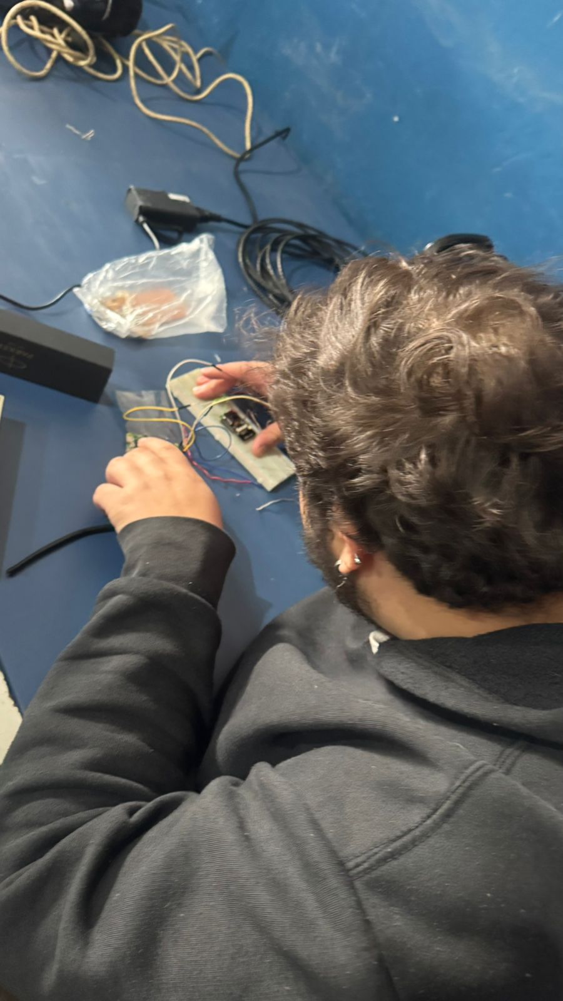
Imagenes/Camara/Prueba de la camara en protoboard.jpg
