impatrq/VIA/Imagenes/Camara/Prueba de reconocimiento.png

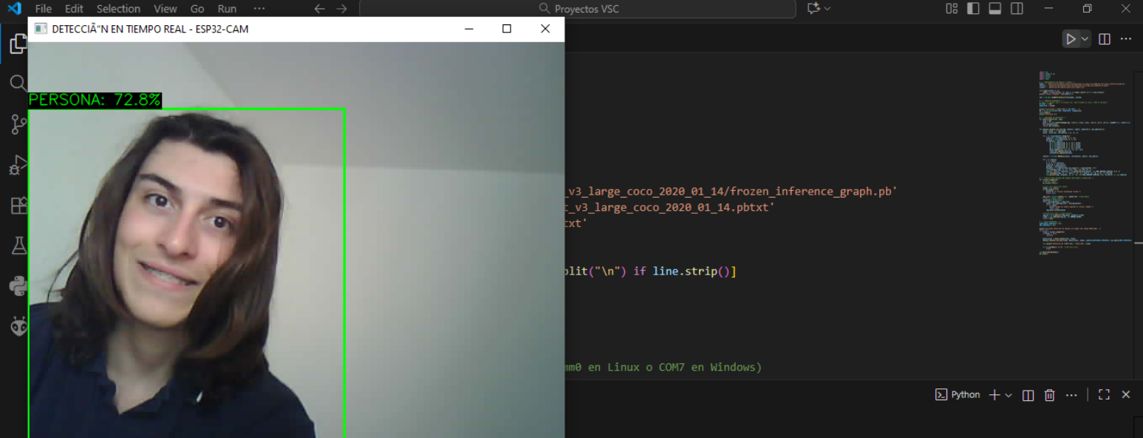
Imagenes/Camara/Prueba de reconocimiento.png
