impatrq/VIA/Imagenes/Pagina web y de asistencia/Pagian de asistencia/Prueba 1 Programación en HTML.png

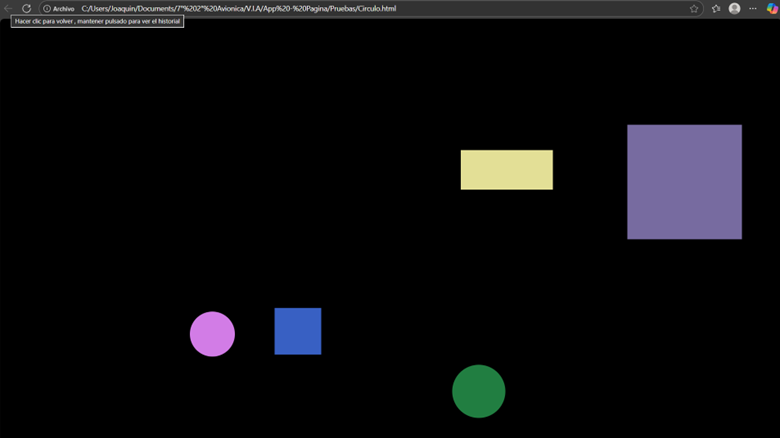
Imagenes/Pagina web y de asistencia/Pagian de asistencia/Prueba 1 Programación en HTML.png
