impatrq/VIA/Imagenes/Pagina web y de asistencia/Pagian de asistencia/Prueba 2 Programación en HTML.png

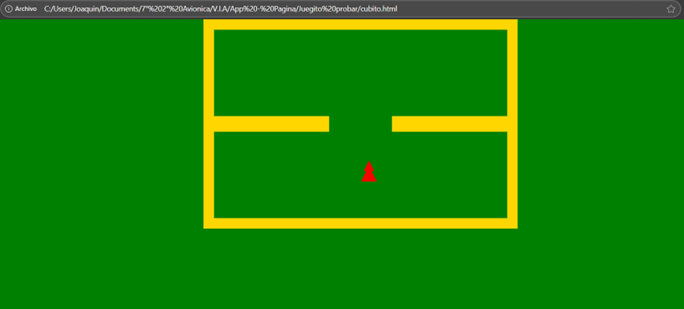
Imagenes/Pagina web y de asistencia/Pagian de asistencia/Prueba 2 Programación en HTML.png
