impatrq/VIA/Imagenes/Proceso/Prueba de sensor de proximidad .jpg

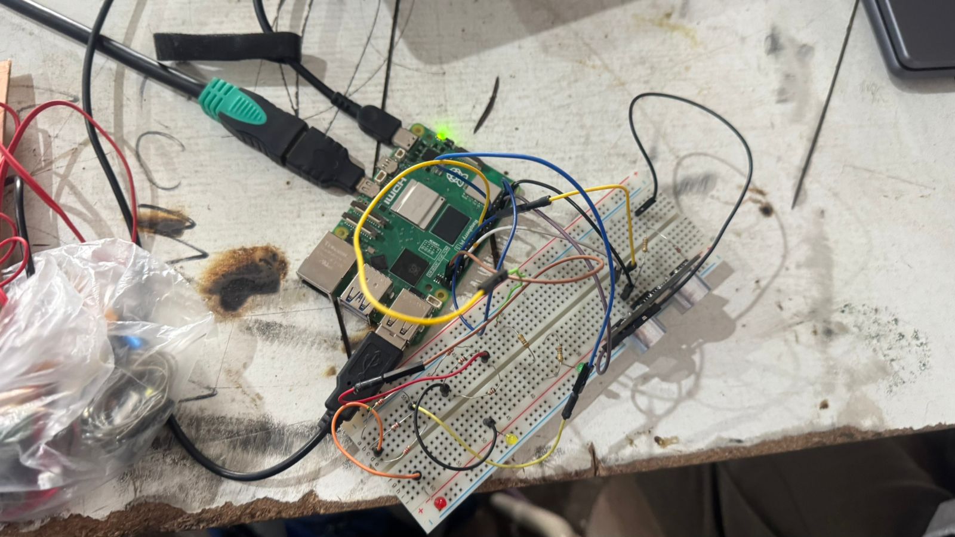
Imagenes/Proceso/Prueba de sensor de proximidad .jpg
