impatrq/VIA/Compras/IMG_3067.jpeg

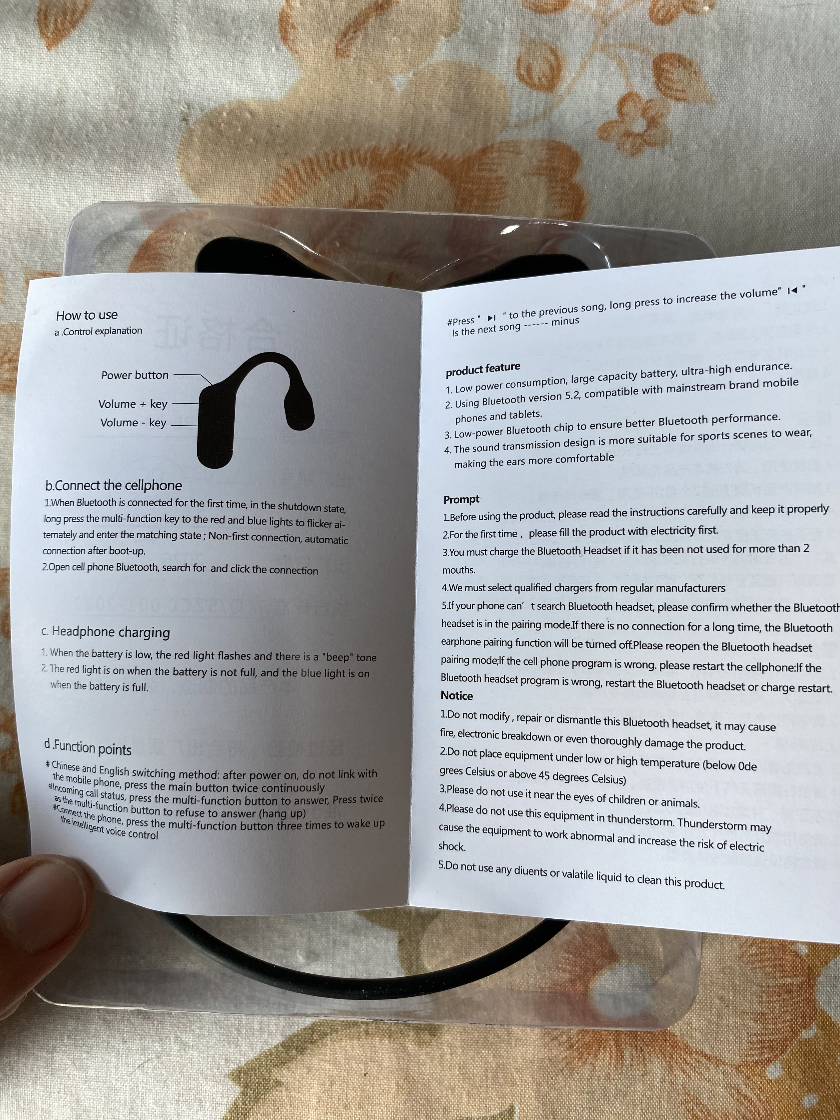
Compras/IMG_3067.jpeg
